individual61/flamingo-repo/Boards/Nano 33 BLE Flamingo/Flamingo Nano 33 BLE Rev 2/Arduino Nano 33 BLE Power Tree.png

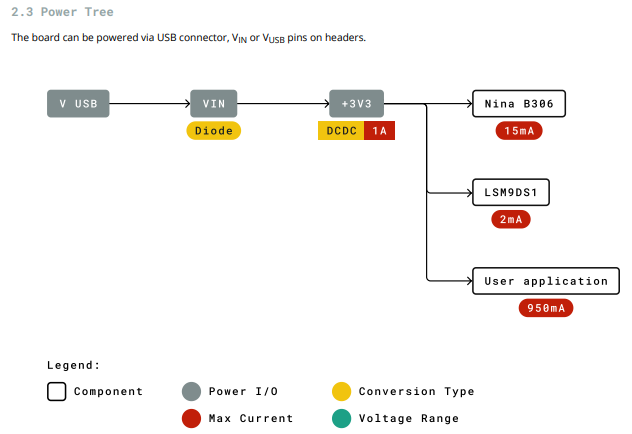
Boards/Nano 33 BLE Flamingo/Flamingo Nano 33 BLE Rev 2/Arduino Nano 33 BLE Power Tree.png
