individual61/flamingo-repo/Boards/Nano 33 BLE Flamingo/Flamingo Nano 33 BLE Rev 2/Nano Power detail 3.png

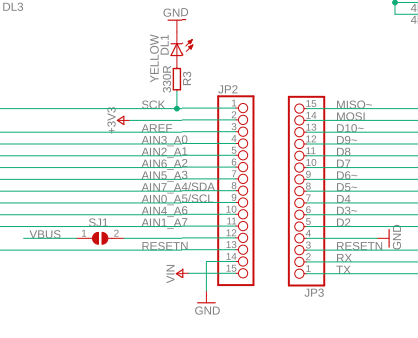
Boards/Nano 33 BLE Flamingo/Flamingo Nano 33 BLE Rev 2/Nano Power detail 3.png
