individual61/flamingo-repo/Boards/Nano 33 BLE Flamingo/Flamingo Nano 33 BLE Rev 2/PDFs/Screenshot 2023-04-27 150545.png

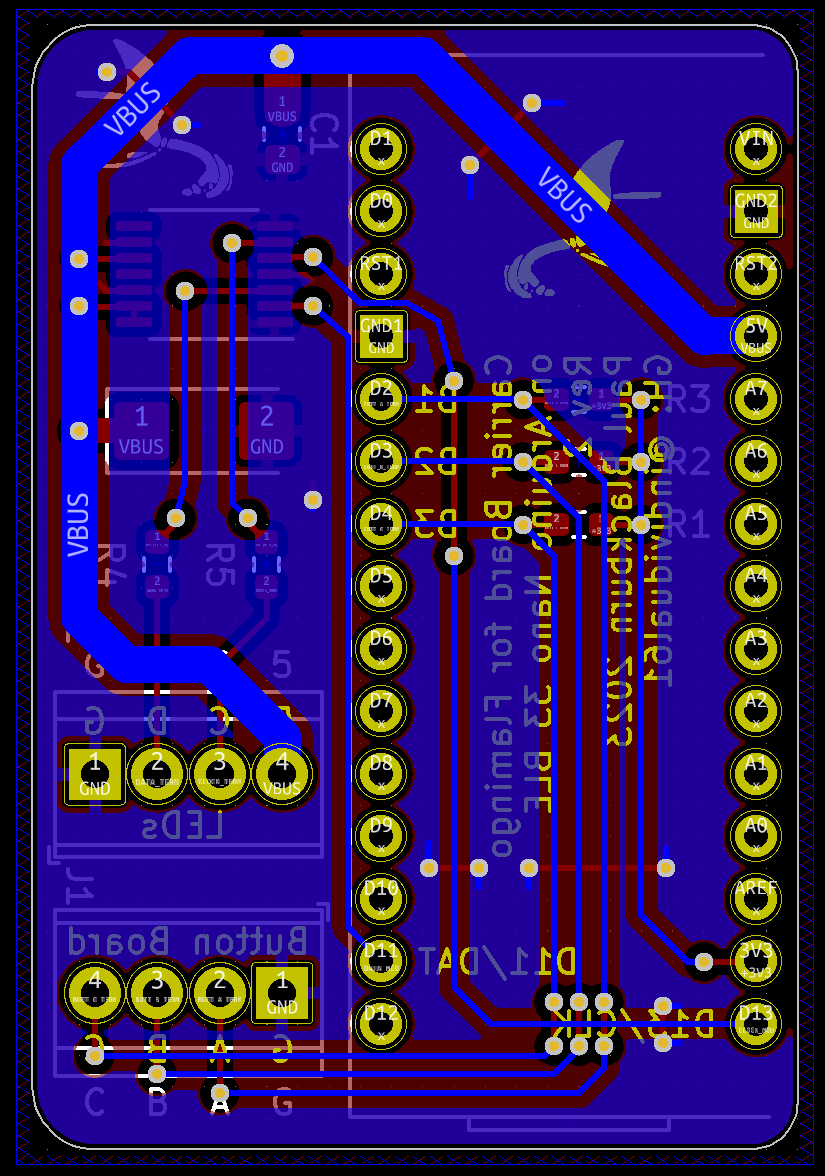
Boards/Nano 33 BLE Flamingo/Flamingo Nano 33 BLE Rev 2/PDFs/Screenshot 2023-04-27 150545.png
