individual61/flamingo-repo/Boards/Nano 33 BLE Flamingo/Flamingo Nano 33 BLE Rev 2/PDFs/Flamingo Nano 33 BLE Rev 2-F_Mask.pdf

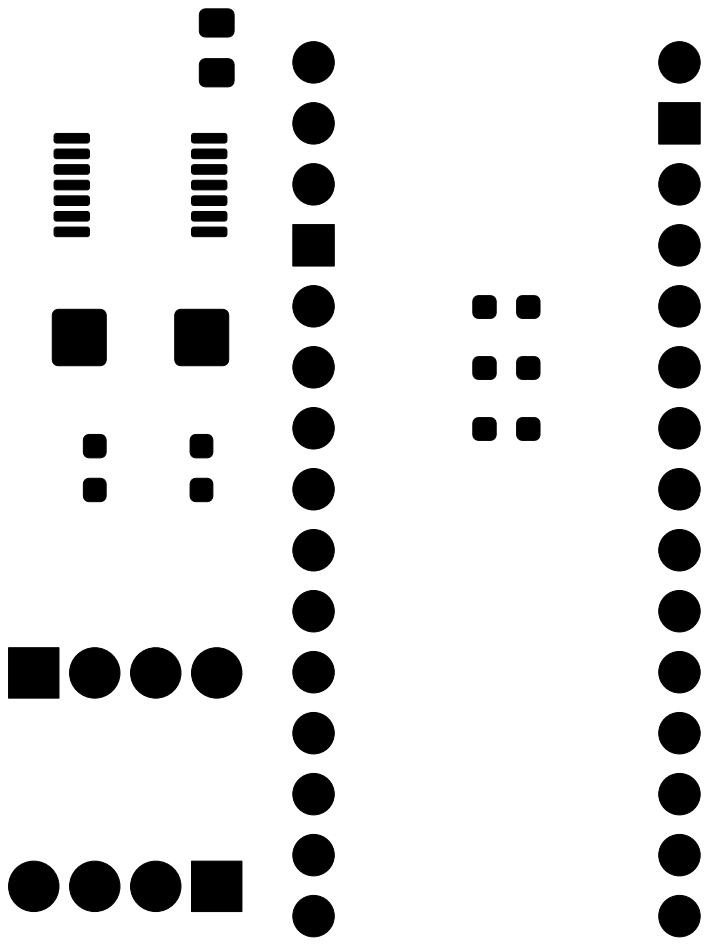
[picture p26: page 1]
