individual61/flamingo-repo/Boards/Nano 33 BLE Flamingo/Flamingo Nano 33 BLE Rev 2/PDFs/Flamingo Nano 33 BLE Rev 2-F_Paste.pdf

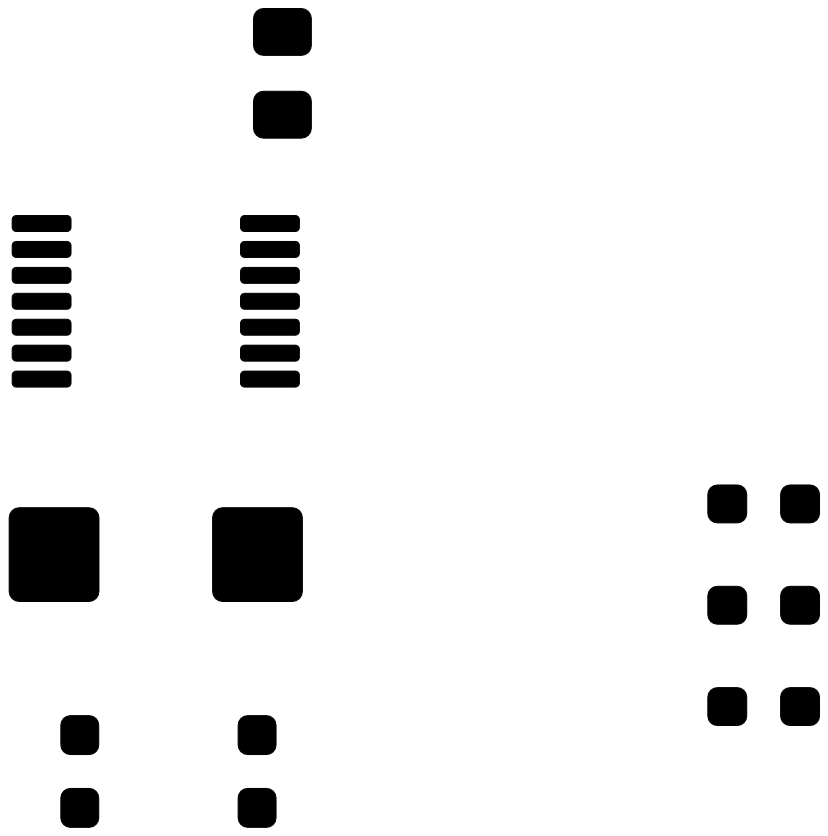
[picture p27: page 1]
