individual61/flamingo-repo/Boards/Nano 33 BLE Flamingo/Flamingo Nano 33 BLE Rev 2/PDFs/Flamingo Nano 33 BLE Rev 2-F_Silkscreen.pdf

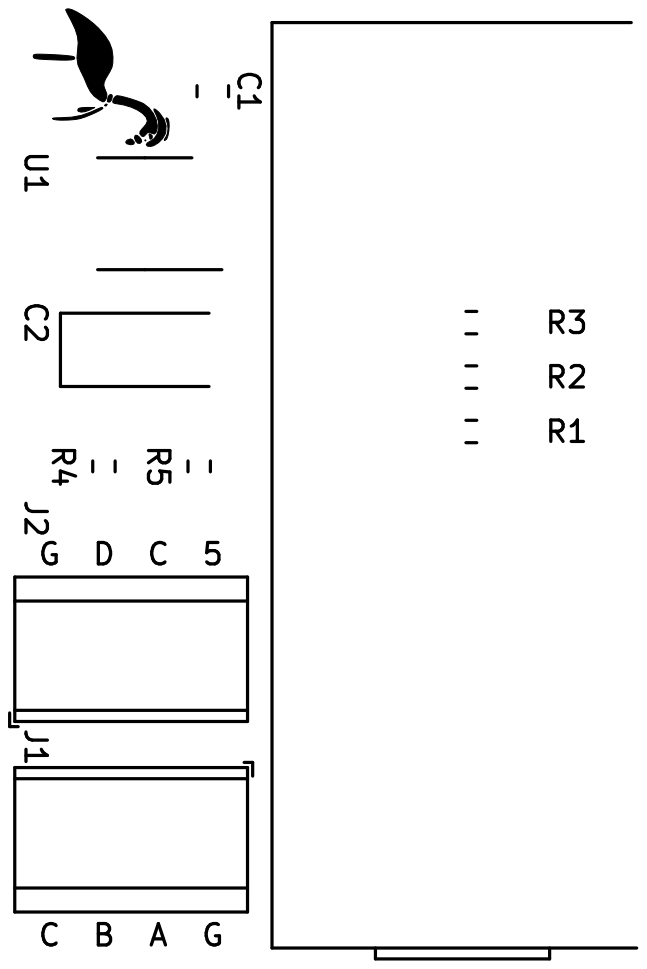
[picture p28: page 1]
