individual61/flamingo-repo/Boards/Flamingo PCBA/Flamingo PCB Rev 3/Flamingo PCB/Power.pdf

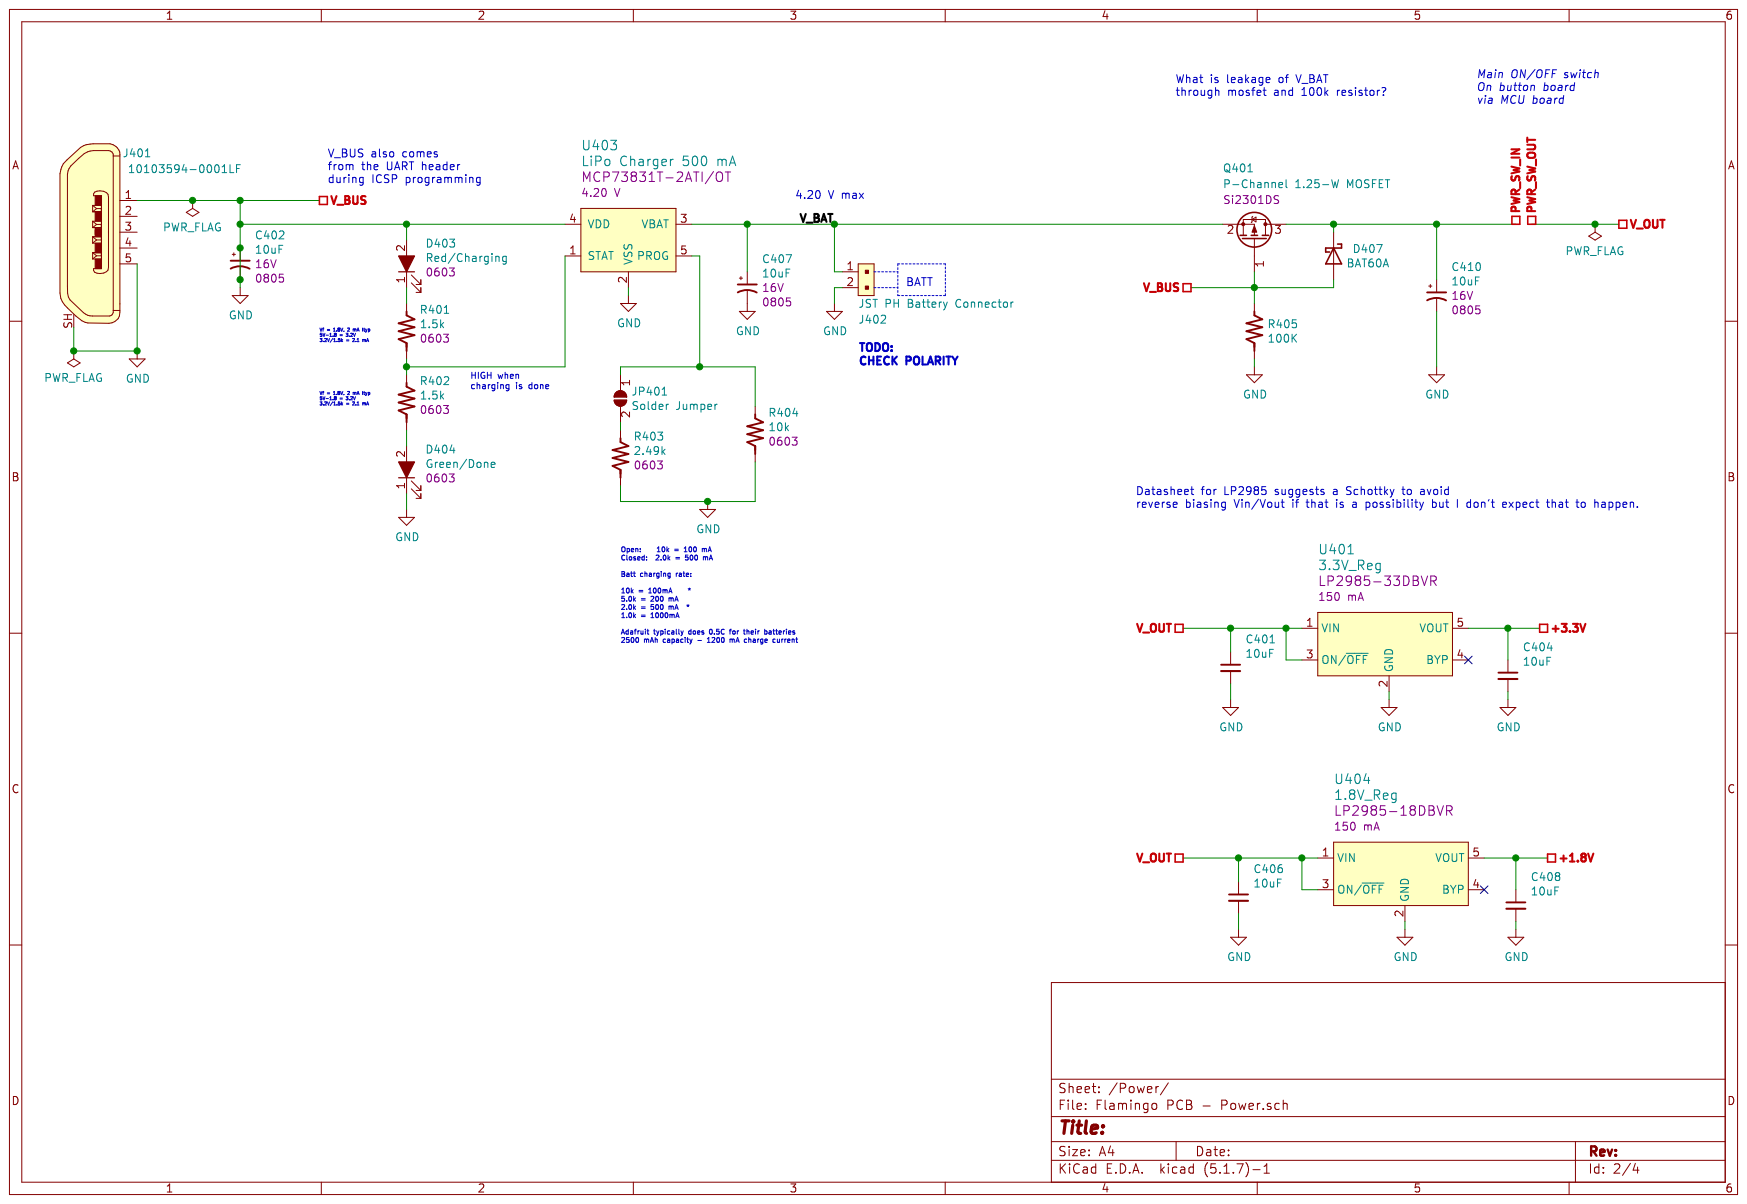
[picture p29: page 1]
