individual61/flamingo-repo/Boards/Flamingo PCBA/Flamingo PCB Rev 3/Flamingo PCB/Flamingo PCB.pdf

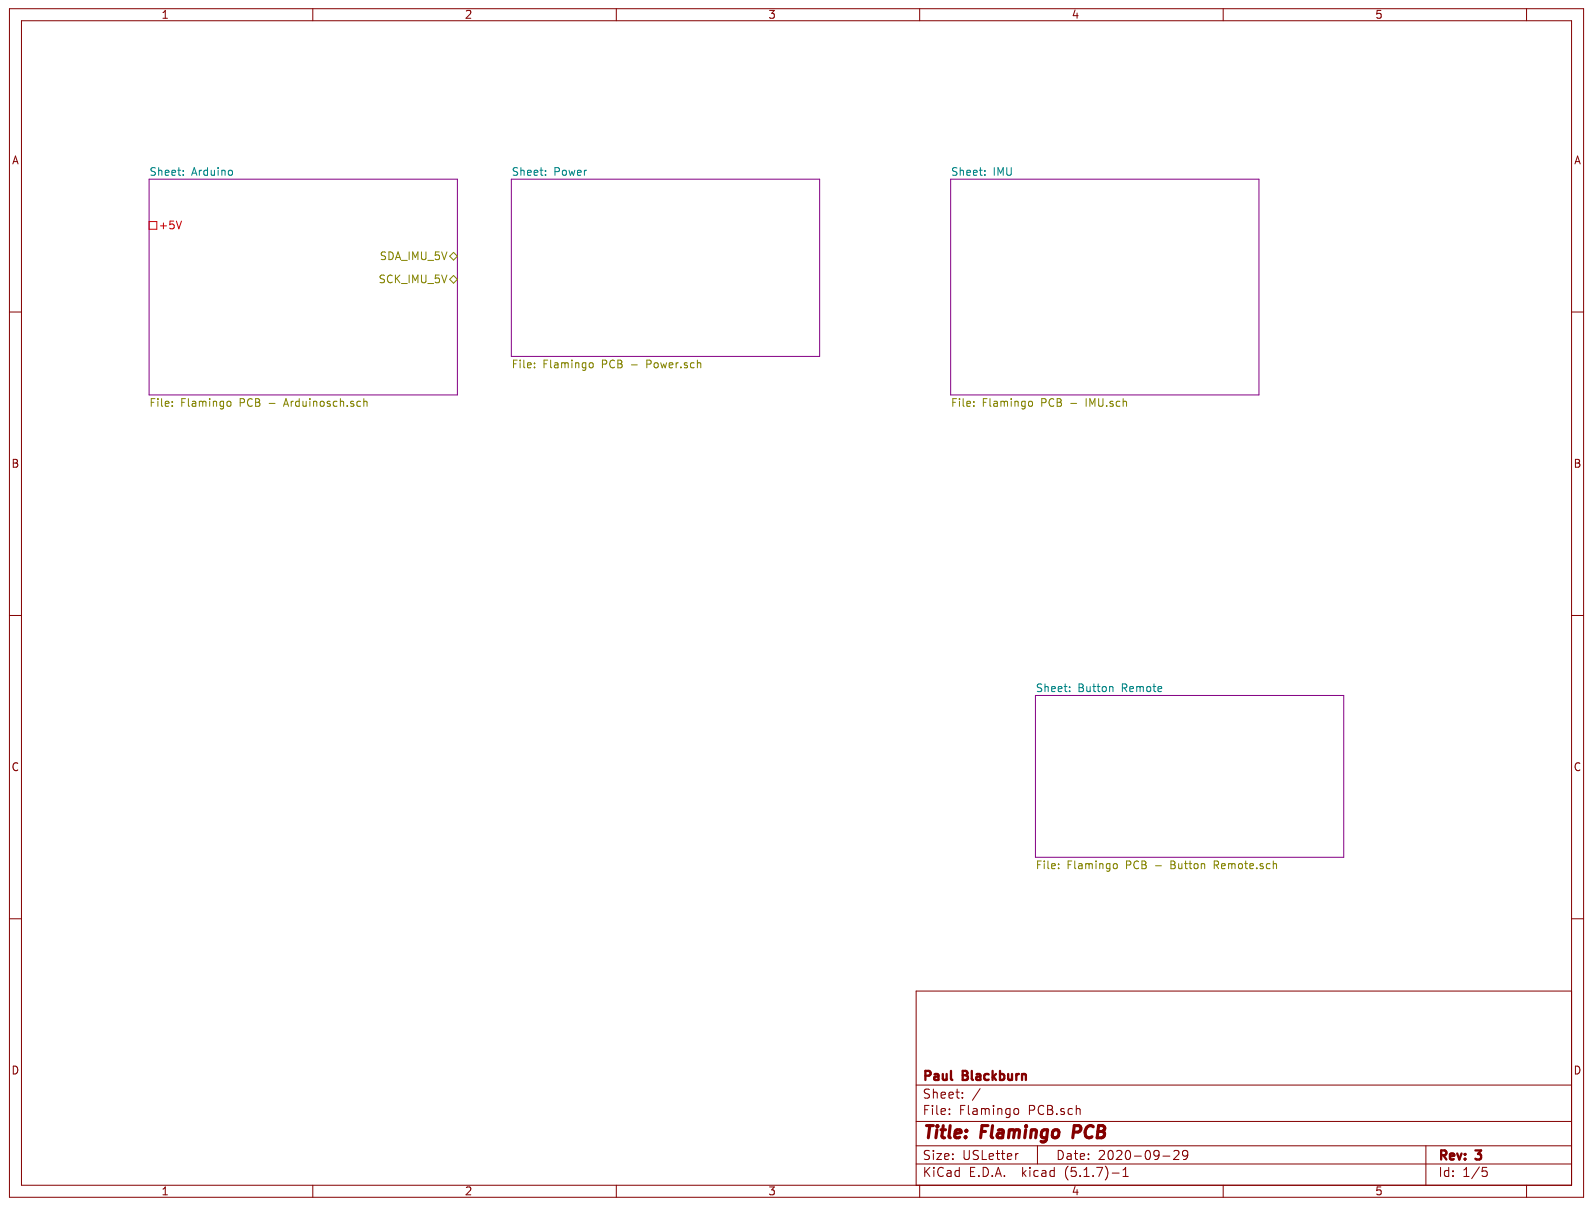
[picture p30: page 1]

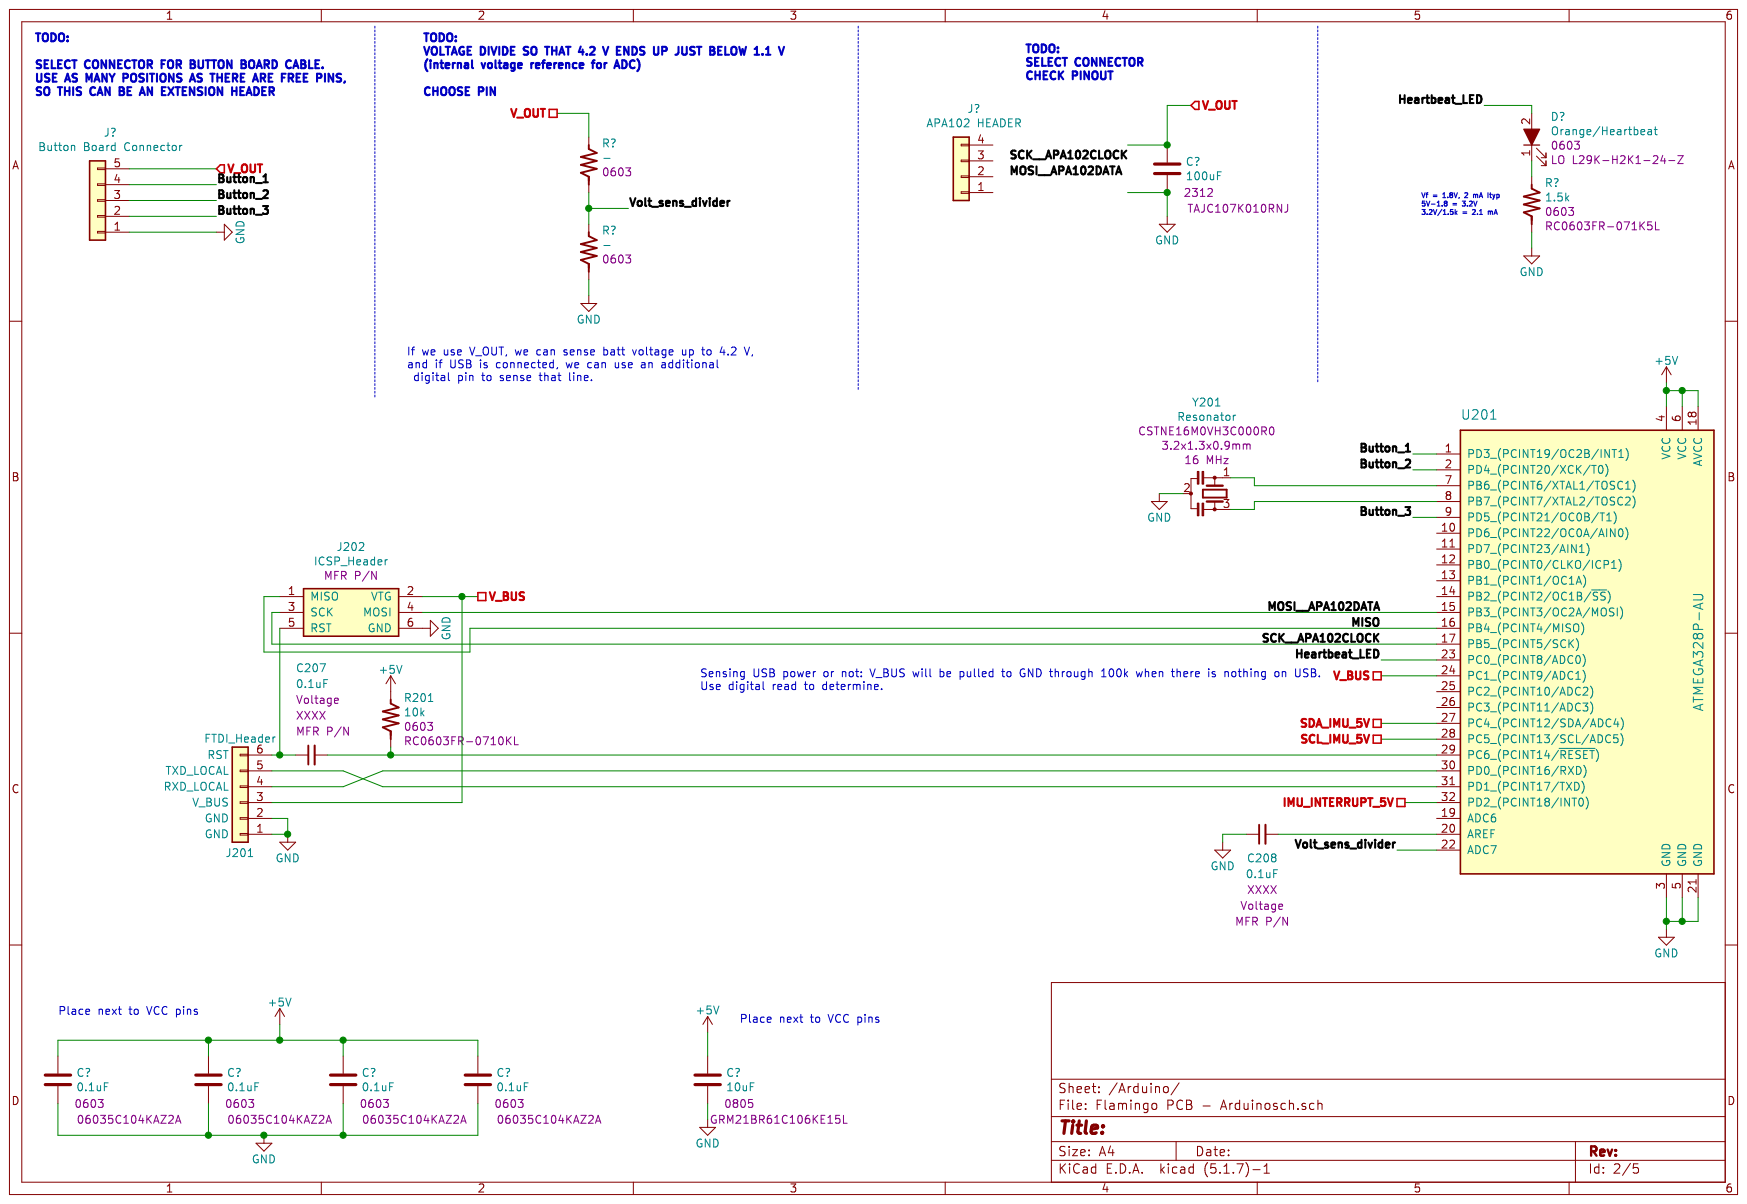
[picture p31: page 2]

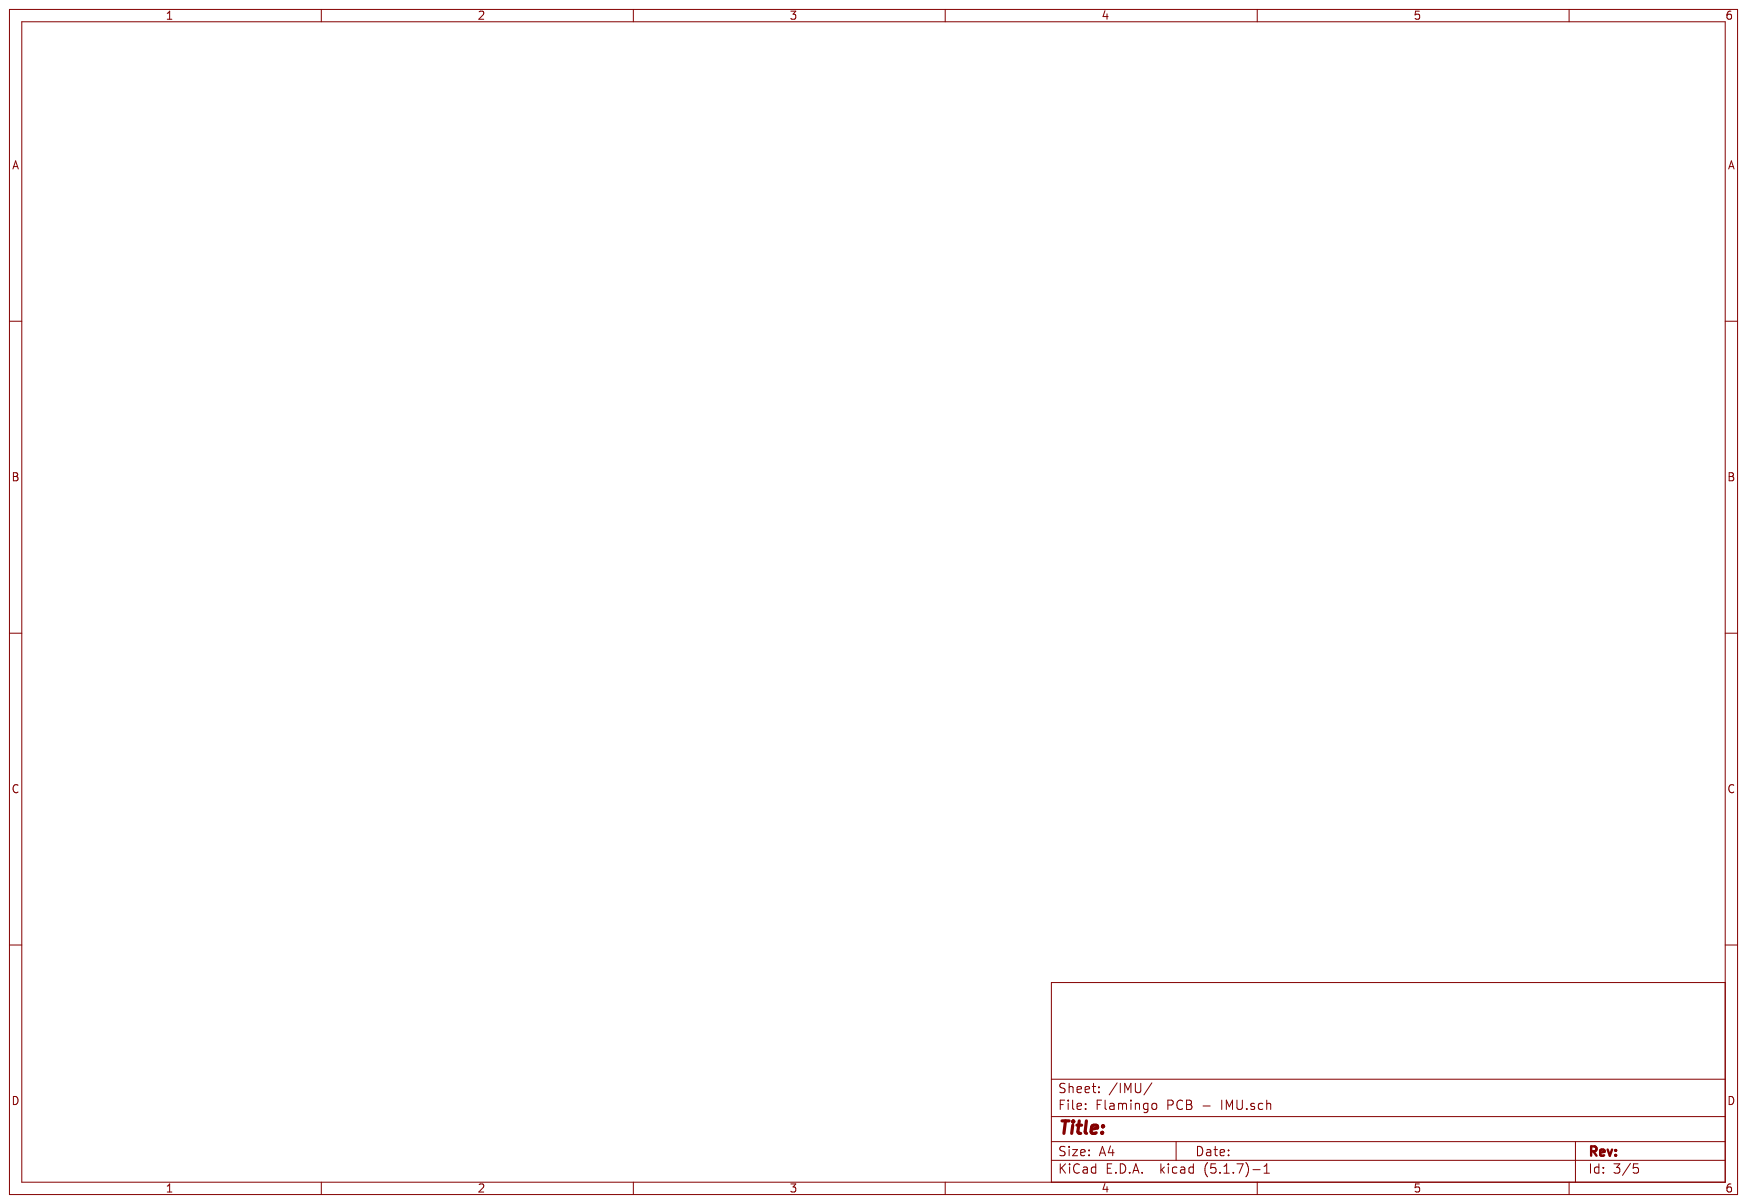
[picture p32: page 3]

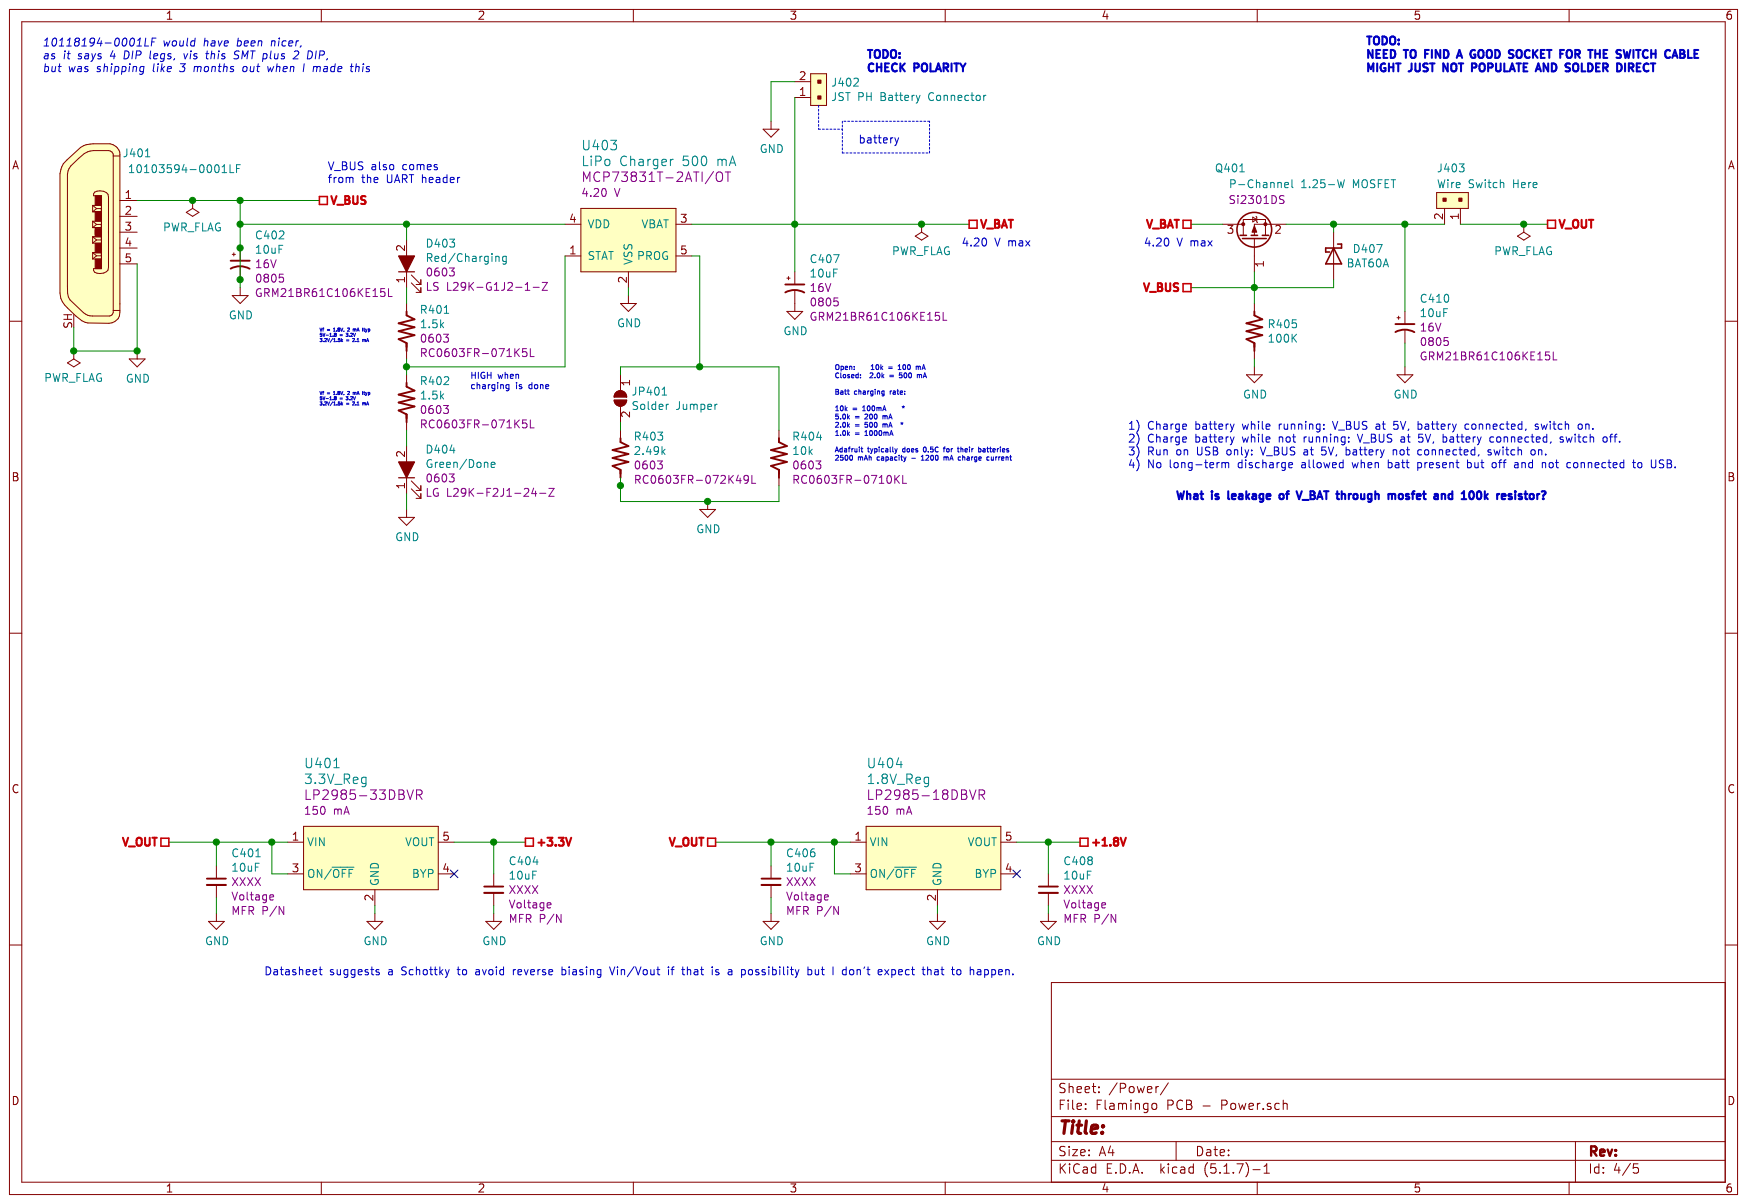
[picture p33: page 4]

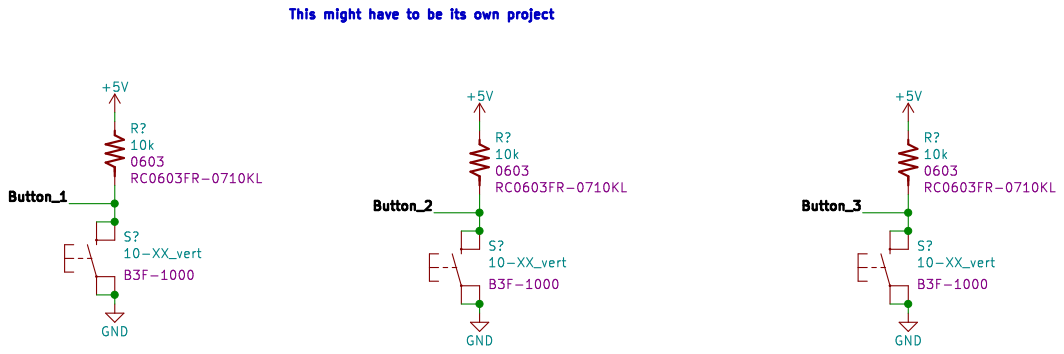
[picture p34: page 5]
