individual61/flamingo-repo/Boards/Bike Flamingo IB-5V-USB/Bike Flamingo IB-5V-USB Rev 1/PDFs/Bike Flamingo for Itsy Bitsy 5V 16MHz, USB Power Rev 1.pdf

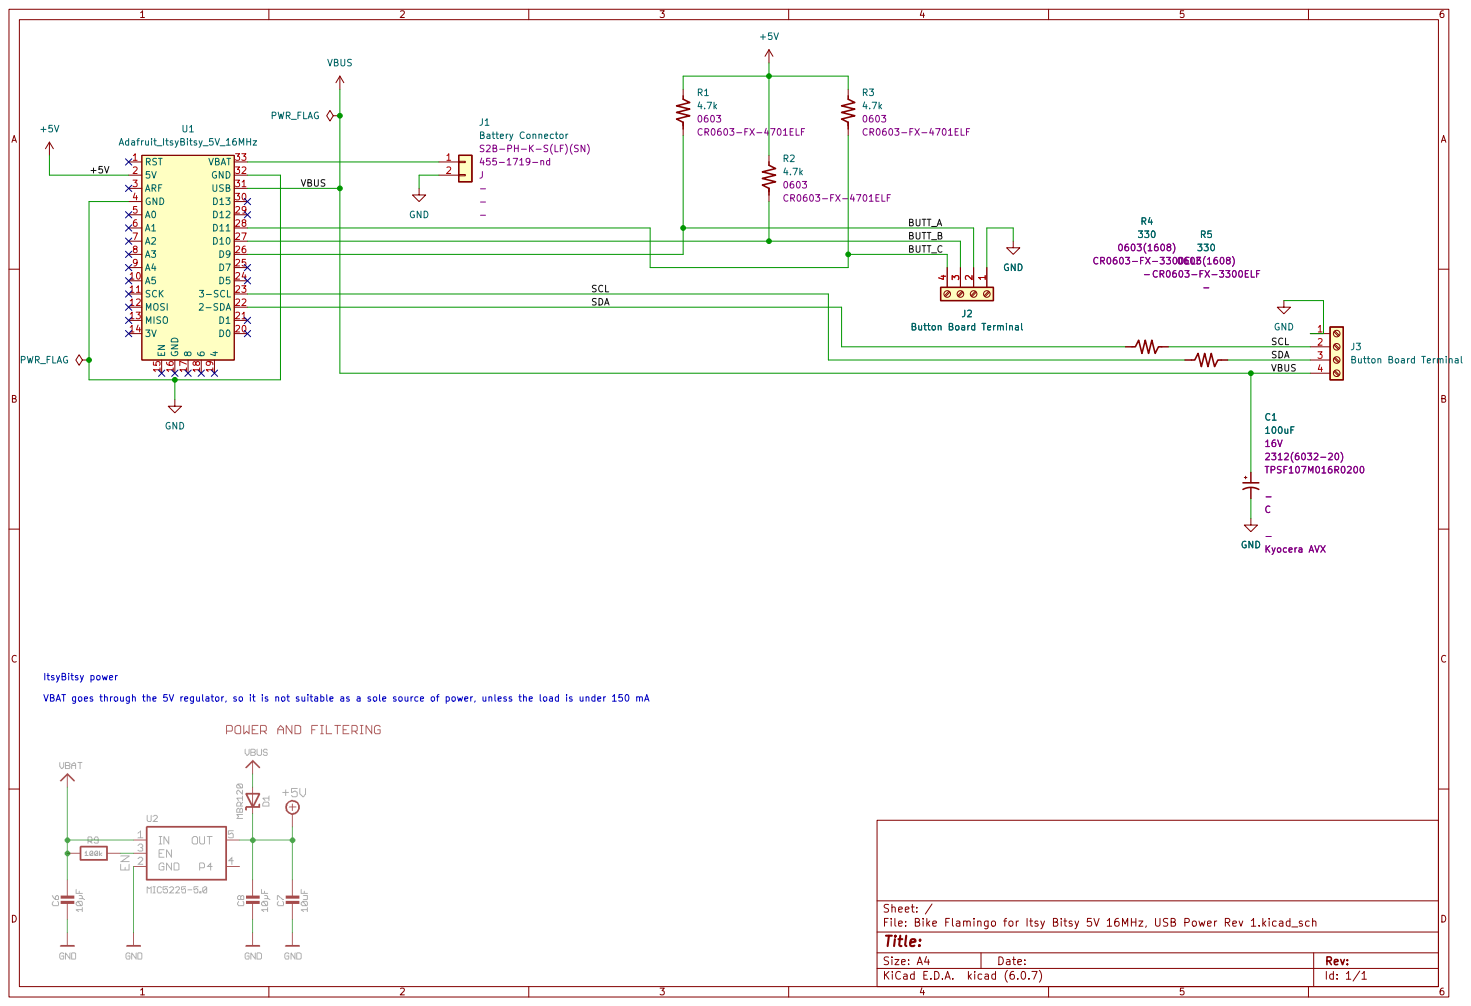
[picture p35: page 1]

Does it make sense to change the LEDs to use VBAT? With VBAT and no USB present, the LEDS get direct battery and the arduino gets regulated output. With USB and no VBAT the LEDs dont see VBUS unless a battery backpack is used. GND

VBAT goes through the 5V regulator, so it is not suitable as a sole source of power, unless the load is under 150 mA
