individual61/flamingo-repo/Boards/Flamingo PCBA/Flamingo PCB Rev 2/inspiration/Adafruit-Pro-Trinket-PCBs-master/Adafruit Pro Trinket 3v3.pdf

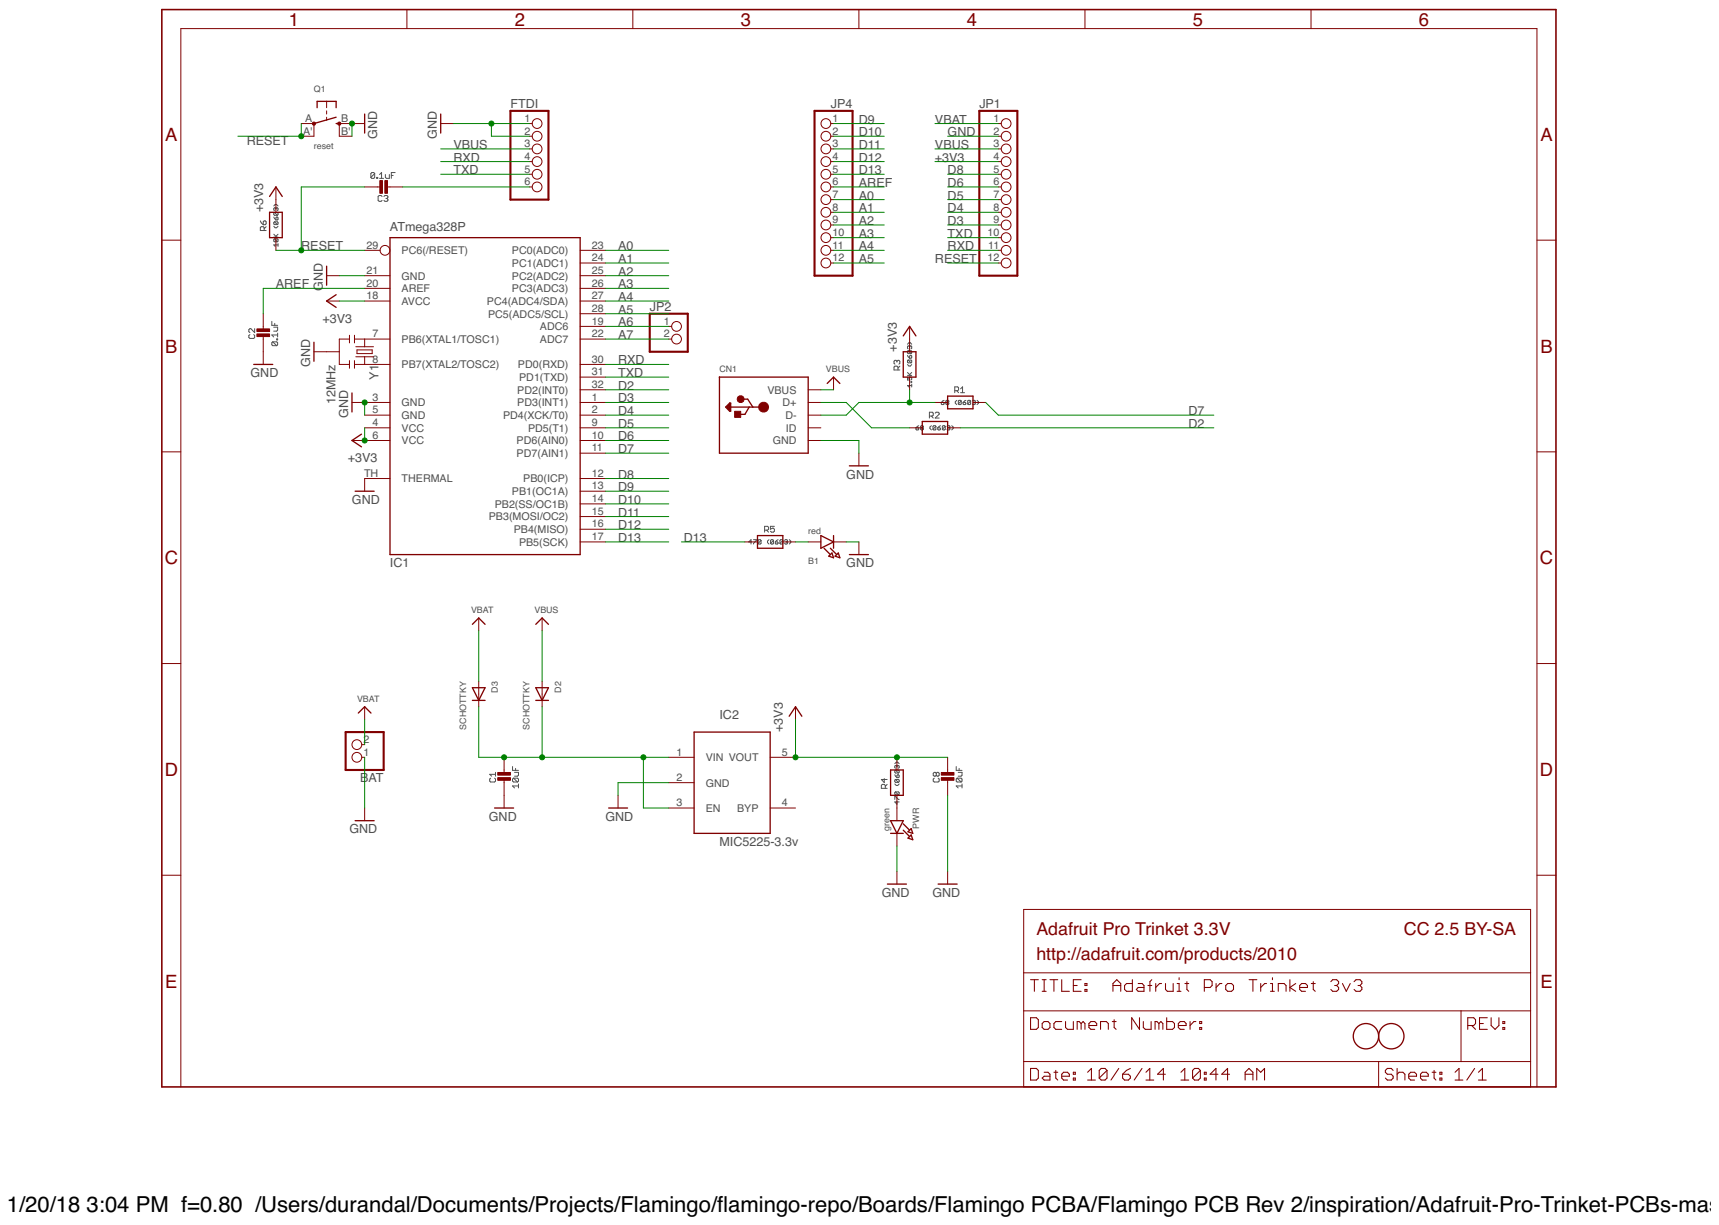
[picture p36: page 1]

Adafruit Pro Trinket 3.3V
http://adafruit.com/products/2010

1/20/18 3:04 PM f=0.80 /Users/durandal/Documents/Projects/Flamingo/flamingo-repo/Boards/Flamingo PCBA/Flamingo PCB Rev 2/inspiration/Adafruit-Pro-Trinket-PCBs-master/Adafruit Pro Trinket 3v3.sch (Sheet: 1/1)
