individual61/flamingo-repo/Boards/Bike Flamingo IB-5V-USB/Bike Flamingo IB-5V-USB Rev 1/PDFs/Board layout.pdf

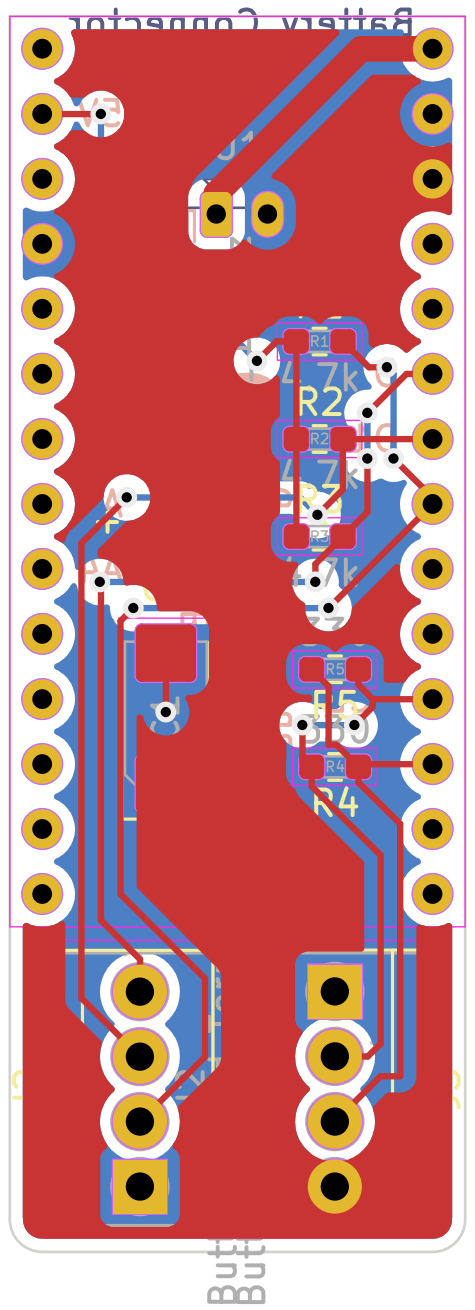
[picture p37: page 1]
