individual61/flamingo-repo/Boards/Flamingo PCBA/Flamingo PCB Rev 1/Flamingo PCB Rev 1.1/Flamingo PCB Rev 1.1.brd

## EAGLE design Boards/Flamingo PCBA/Flamingo PCB Rev 1/Flamingo PCB Rev 1.1/Flamingo PCB Rev 1.1.brd (2017-07-29, an earlier design)

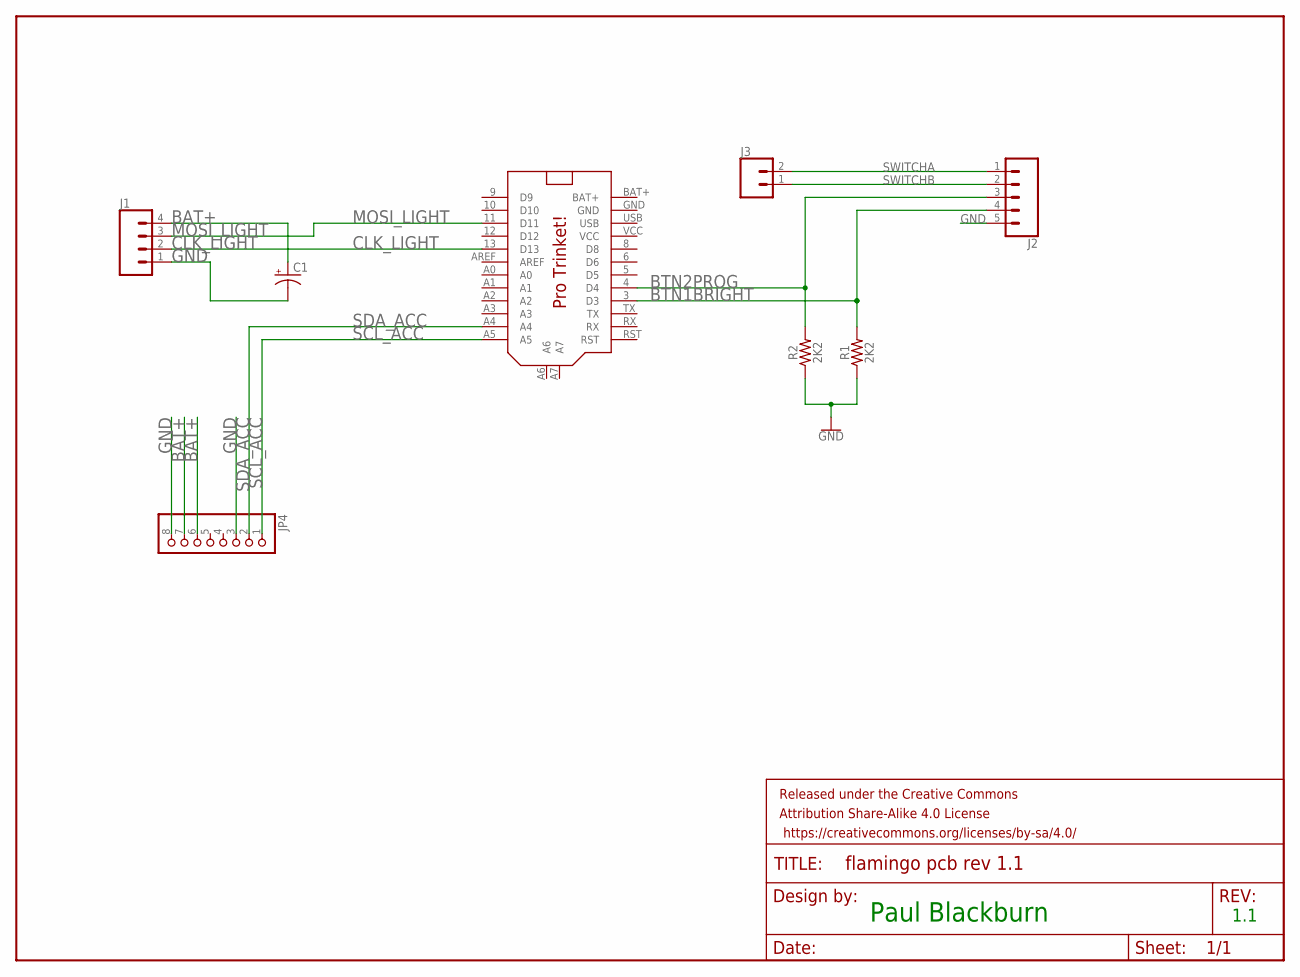
[picture p60: schematic Flamingo PCB Rev 1.1.sch]

Parts:
C1: CPOL-USE5-6; E5-6
FRAME1: FRAME-LETTER; CREATIVE_COMMONS
J1: CONN_04; 1X04
J2: CONN_05; 1X05
J3: CONN_02; 1X02
JP4: PINHD-1X8CLEANBIG; 1X08-CLEANBIG
R1, R2: 2K2; AXIAL-0.3
U$1: PRO_TRINKET; PROTRINKET

Connections:
BAT+: C1.+, J1.4, JP4.6, JP4.7, U$1.BAT+
BTN1BRIGHT: J2.4, R1.P$2 (2), U$1.3 (D3)
BTN2PROG: J2.3, R2.P$2 (2), U$1.4 (D4)
CLK_LIGHT: J1.2, U$1.13 (D13)
GND: C1.-, J1.1, J2.5, JP4.3, JP4.8, R1.P$1 (1), R2.P$1 (1), U$1.GND
MOSI_LIGHT: J1.3, U$1.11 (D11)
SCL_ACC: JP4.1, U$1.A5
SDA_ACC: JP4.2, U$1.A4
SWITCHA: J2.1, J3.2
SWITCHB: J2.2, J3.1
USB: U$1.USB
VCC: U$1.VCC

Notes on the sheet:
Paul Blackburn
1.1

Board: 2 copper layers, 9 parts (0 on the bottom side), 10 nets, no tracks yet.
