individual61/flamingo-repo/Boards/Pixelblaze Flamingo/Ref/PB32_3.x.brd

## EAGLE design Boards/Pixelblaze Flamingo/Ref/PB32_3.x.brd (2023-04-28)

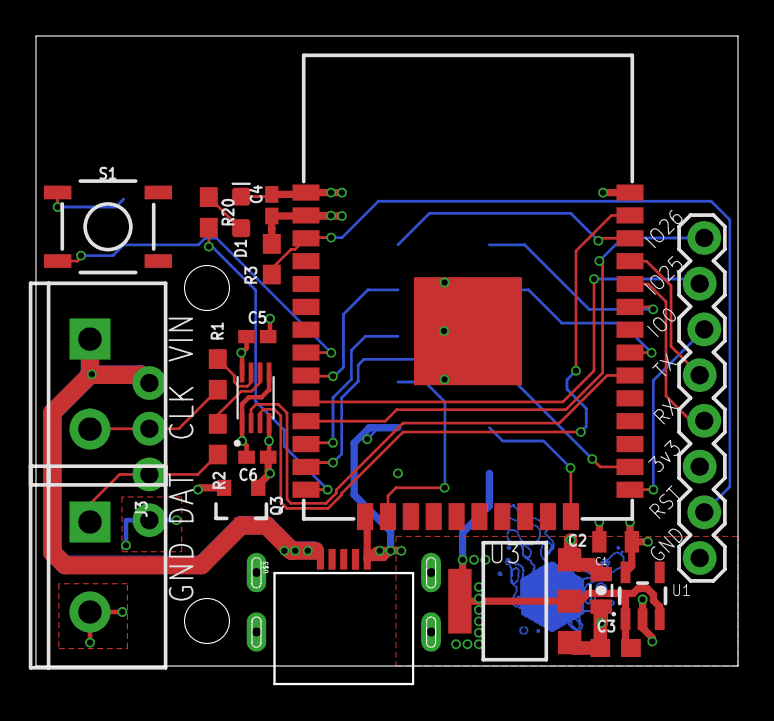
[picture p61: board PB32_3.x.brd from above]

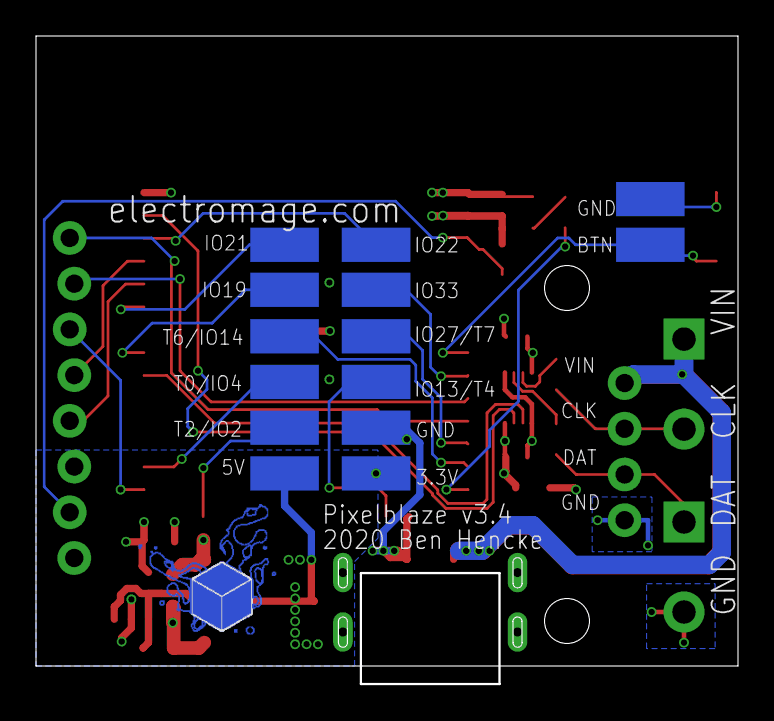
[picture p62: board PB32_3.x.brd from below]

Board: 4 copper layers, 39.0 x 36.0 mm, 37 parts (15 on the bottom side), 29 nets.

Parts:
C1: 1.0uF; 0805-CAP
C2: 10uF; 0805
C3: 4.7uF; 0603
C4, C5, C6: 0.1uF; C0402K
D1: LED-0603
GP1, GP3, GP6, GP8, GP9: PAD
IO2, IO4, IO13, IO14, IO19, IO21, IO22, IO27, IO33: PAD
J1: 1X08_LOCK
J2, J3: SCREWTERMINAL-5MM-2
J4: 1X04_NO_SILK
Q3: 2.5A/30V/105mΩ; SOT23-3
R1, R2, R20: 100; 0603
R3: 1k; 0603
S1: MOMENTARY-SWITCH-SPST-SMD-5.2MM; TACTILE_SWITCH_SMD_5.2MM
U1: AP2112K-3.3TRG1; SOT23-5
U2: ESP-WROOM-32
U3: NX1117C15Z; SOT223
U$1: SN74LVC2T45DCUR; SOP50P310X90-8N
U$2: ELECTRO_MAGE_PCB4_PIXEL_2#PNG
U$3: USB-CON-5PINUSB-SUNK-TIGHT; USB-SUNK-TIGHT

Connections:
+3V3: C2.1, C4.1, C6.1, GP1.P$1, J1.3, R3.2, U1.5, U2.2, U$1.1, U$1.5
+5V: C3.1, C5.1, GP6.P$1, U1.1, U1.3, U3.2, U3.4, U$1.8
BUTTON: GP8.P$1, S1.3, U2.8
EN: J1.2, R3.1, U2.3
GND: C1.2, C2.2, C3.2, C4.2, C5.2, C6.2, D1.C, GP3.P$1, GP9.P$1, J1.1, J3.2, J4.1, Q3.1, S1.1, U1.2, U2.1, U2.15, U2.38, U2.GND, U3.1, U$1.4, U$3.5
IO0: J1.6, U2.25
IO2: IO2.P$1, U2.24
IO4: IO4.P$1, U2.26
IO13: IO13.P$1, U2.16
IO14: IO14.P$1, U2.13
IO19: IO19.P$1, U2.31
IO21: IO21.P$1, U2.33
IO22: IO22.P$1, U2.36
IO25: J1.7, U2.10
IO26: J1.8, U2.11
IO27: IO27.P$1, U2.12
IO33: IO33.P$1, U2.9
LED: R20.2, U2.14
MOSI: U2.37, U$1.3
MOSI_OUT: J3.1, J4.2, R2.2
unnamed: C1.1, Q3.2, U3.3
unnamed: R1.1, U$1.7
unnamed: R2.1, U$1.6
unnamed: D1.A, R20.1
RX: J1.4, U2.34
SCK: U2.30, U$1.2
SCK_OUT: J2.2, J4.3, R1.2
TX: J1.5, U2.35
VIN: J2.1, J4.4, Q3.3, U$3.1
