individual61/flamingo-repo/Boards/Flamingo PCBA/Flamingo PCB Rev 2/inspiration/LiPower_Boost_Converter-master/Production Files/Li_Power_Boost_Converter-Panel-v12B.brd

## EAGLE design Boards/Flamingo PCBA/Flamingo PCB Rev 2/inspiration/LiPower_Boost_Converter-master/Production Files/Li_Power_Boost_Converter-Panel-v12B.brd (2018-02-05, an earlier design)

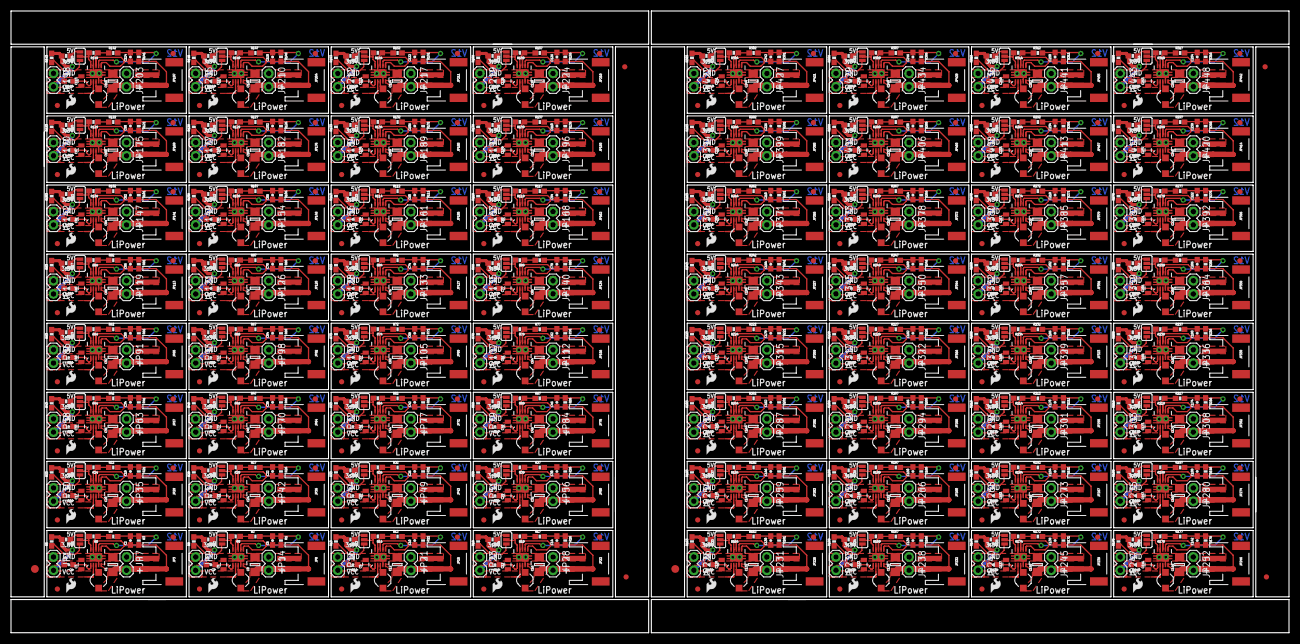
[picture p63: board Li_Power_Boost_Converter-Panel-v12B.brd from above]

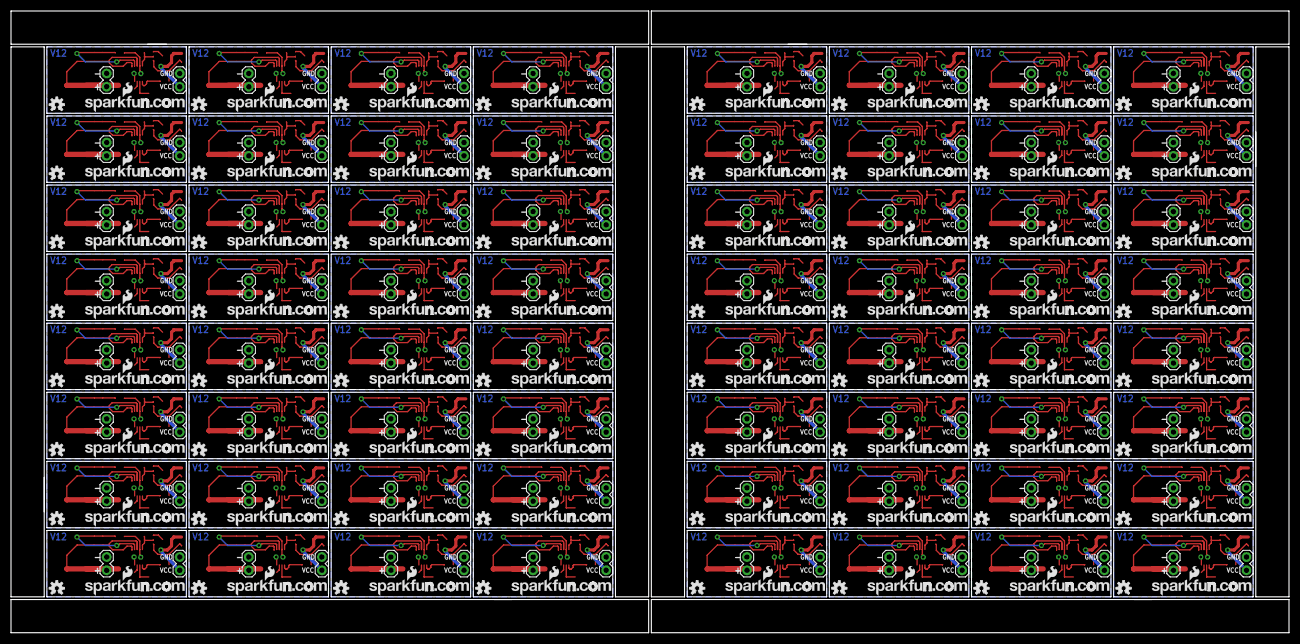
[picture p64: board Li_Power_Boost_Converter-Panel-v12B.brd from below]

Board: 2 copper layers, 244.3 x 118.9 mm, 1286 parts (128 on the bottom side), 576 nets.

Parts:
C1, C8, C12, C16, C20, C24, C28, C32, C36, C40, C44, C48, C52, C56, C60, C64, C68, C72, C76, C80, C84, C88, C92, C96, C100, C104, C108, C112, C116, C120, C124, C128, C132, C136, C140, C144, C148, C152, C156, C160, C164, C168, C172, C176, C180, C184, C188, C192, C196, C200, C204, C208, C212, C216, C220, C224, C228, C232, C236, C240, C244, C248, C252, C256: 10uF; 1206
C2, C4, C6, C7, C10, C11, C14, C15, C18, C19, C22, C23, C26, C27, C30, C31, C34, C35, C38, C39, C42, C43, C46, C47, C50, C51, C54, C55, C58, C59, C62, C63, C66, C67, C70, C71, C74, C75, C78, C79, C82, C83, C86, C87, C90, C91, C94, C95, C98, C99, C102, C103, C106, C107, C110, C111, C114, C115, C118, C119, C122, C123, C126, C127, C130, C131, C134, C135, C138, C139, C142, C143, C146, C147, C150, C151, C154, C155, C158, C159, C162, C163, C166, C167, C170, C171, C174, C175, C178, C179, C182, C183, C186, C187, C190, C191, C194, C195, C198, C199, C202, C203, C206, C207, C210, C211, C214, C215, C218, C219, C222, C223, C226, C227, C230, C231, C234, C235, C238, C239, C242, C243, C246, C247, C250, C251, C254, C255: 0.1uF; 0603-CAP
C3, C5, C9, C13, C17, C21, C25, C29, C33, C37, C41, C45, C49, C53, C57, C61, C65, C69, C73, C77, C81, C85, C89, C93, C97, C101, C105, C109, C113, C117, C121, C125, C129, C133, C137, C141, C145, C149, C153, C157, C161, C165, C169, C173, C177, C181, C185, C189, C193, C197, C201, C205, C209, C213, C217, C221, C225, C229, C233, C237, C241, C245, C249, C253: 22uF; 0805
E$1, E$6: FIDUCIAL-1.5X3
E$2, E$3, E$4, E$5: FIDUCIAL-1X2
JP1, JP9, JP16, JP23, JP30, JP37, JP44, JP51, JP58, JP65, JP72, JP79, JP86, JP93, JP100, JP107, JP114, JP121, JP128, JP135, JP142, JP149, JP156, JP163, JP170, JP177, JP184, JP191, JP198, JP205, JP212, JP219, JP226, JP233, JP240, JP247, JP254, JP261, JP268, JP275, JP282, JP289, JP296, JP303, JP310, JP317, JP324, JP331, JP338, JP345, JP352, JP359, JP366, JP373, JP380, JP387, JP394, JP401, JP408, JP415, JP422, JP429, JP436, JP443: VOUT; 1X02
JP2, JP10, JP17, JP24, JP31, JP38, JP45, JP52, JP59, JP66, JP73, JP80, JP87, JP94, JP101, JP108, JP115, JP122, JP129, JP136, JP143, JP150, JP157, JP164, JP171, JP178, JP185, JP192, JP199, JP206, JP213, JP220, JP227, JP234, JP241, JP248, JP255, JP262, JP269, JP276, JP283, JP290, JP297, JP304, JP311, JP318, JP325, JP332, JP339, JP346, JP353, JP360, JP367, JP374, JP381, JP388, JP395, JP402, JP409, JP416, JP423, JP430, JP437, JP444: LOGO-SFESK; SFE-LOGO-FLAME
JP3, JP8, JP15, JP22, JP29, JP36, JP43, JP50, JP57, JP64, JP71, JP78, JP85, JP92, JP99, JP106, JP113, JP120, JP127, JP134, JP141, JP148, JP155, JP162, JP169, JP176, JP183, JP190, JP197, JP204, JP211, JP218, JP225, JP232, JP239, JP246, JP253, JP260, JP267, JP274, JP281, JP288, JP295, JP302, JP309, JP316, JP323, JP330, JP337, JP344, JP351, JP358, JP365, JP372, JP379, JP386, JP393, JP400, JP407, JP414, JP421, JP428, JP435, JP442: JST; JST-2-SMD
JP4, JP5, JP11, JP12, JP18, JP19, JP25, JP26, JP32, JP33, JP39, JP40, JP46, JP47, JP53, JP54, JP60, JP61, JP67, JP68, JP74, JP75, JP81, JP82, JP88, JP89, JP95, JP96, JP102, JP103, JP109, JP110, JP116, JP117, JP123, JP124, JP130, JP131, JP137, JP138, JP144, JP145, JP151, JP152, JP158, JP159, JP165, JP166, JP172, JP173, JP179, JP180, JP186, JP187, JP193, JP194, JP200, JP201, JP207, JP208, JP214, JP215, JP221, JP222, JP228, JP229, JP235, JP236, JP242, JP243, JP249, JP250, JP256, JP257, JP263, JP264, JP270, JP271, JP277, JP278, JP284, JP285, JP291, JP292, JP298, JP299, JP305, JP306, JP312, JP313, JP319, JP320, JP326, JP327, JP333, JP334, JP340, JP341, JP347, JP348, JP354, JP355, JP361, JP362, JP368, JP369, JP375, JP376, JP382, JP383, JP389, JP390, JP396, JP397, JP403, JP404, JP410, JP411, JP417, JP418, JP424, JP425, JP431, JP432, JP438, JP439, JP445, JP446: FIDUCIAL1X2; FIDUCIAL-1X2
JP6, JP13, JP20, JP27, JP34, JP41, JP48, JP55, JP62, JP69, JP76, JP83, JP90, JP97, JP104, JP111, JP118, JP125, JP132, JP139, JP146, JP153, JP160, JP167, JP174, JP181, JP188, JP195, JP202, JP209, JP216, JP223, JP230, JP237, JP244, JP251, JP258, JP265, JP272, JP279, JP286, JP293, JP300, JP307, JP314, JP321, JP328, JP335, JP342, JP349, JP356, JP363, JP370, JP377, JP384, JP391, JP398, JP405, JP412, JP419, JP426, JP433, JP440, JP447: LOGO-SFENEW; SFE-NEW-WEBLOGO
JP7, JP14, JP21, JP28, JP35, JP42, JP49, JP56, JP63, JP70, JP77, JP84, JP91, JP98, JP105, JP112, JP119, JP126, JP133, JP140, JP147, JP154, JP161, JP168, JP175, JP182, JP189, JP196, JP203, JP210, JP217, JP224, JP231, JP238, JP245, JP252, JP259, JP266, JP273, JP280, JP287, JP294, JP301, JP308, JP315, JP322, JP329, JP336, JP343, JP350, JP357, JP364, JP371, JP378, JP385, JP392, JP399, JP406, JP413, JP420, JP427, JP434, JP441, JP448: VIN; 1X02
L1, L2, L3, L4, L5, L6, L7, L8, L9, L10, L11, L12, L13, L14, L15, L16, L17, L18, L19, L20, L21, L22, L23, L24, L25, L26, L27, L28, L29, L30, L31, L32, L33, L34, L35, L36, L37, L38, L39, L40, L41, L42, L43, L44, L45, L46, L47, L48, L49, L50, L51, L52, L53, L54, L55, L56, L57, L58, L59, L60, L61, L62, L63, L64: 4.7uH, 1.2A; CDRH2D09
R1, R3, R7, R10, R11, R15, R16, R20, R21, R25, R26, R30, R31, R35, R36, R40, R41, R45, R46, R50, R51, R55, R56, R60, R61, R65, R66, R70, R71, R75, R76, R80, R81, R85, R86, R90, R91, R95, R96, R100, R101, R105, R106, R110, R111, R115, R116, R120, R121, R125, R126, R130, R131, R135, R136, R140, R141, R145, R146, R150, R151, R155, R156, R160, R161, R165, R166, R170, R171, R175, R176, R180, R181, R185, R186, R190, R191, R195, R196, R200, R201, R205, R206, R210, R211, R215, R216, R220, R221, R225, R226, R230, R231, R235, R236, R240, R241, R245, R246, R250, R251, R255, R256, R260, R261, R265, R266, R270, R271, R275, R276, R280, R281, R285, R286, R290, R291, R295, R296, R300, R301, R305, R306, R310, R311, R315, R316, R320: 2M; 0603-RES
R2, R4, R6, R9, R12, R14, R17, R19, R22, R24, R27, R29, R32, R34, R37, R39, R42, R44, R47, R49, R52, R54, R57, R59, R62, R64, R67, R69, R72, R74, R77, R79, R82, R84, R87, R89, R92, R94, R97, R99, R102, R104, R107, R109, R112, R114, R117, R119, R122, R124, R127, R129, R132, R134, R137, R139, R142, R144, R147, R149, R152, R154, R157, R159, R162, R164, R167, R169, R172, R174, R177, R179, R182, R184, R187, R189, R192, R194, R197, R199, R202, R204, R207, R209, R212, R214, R217, R219, R222, R224, R227, R229, R232, R234, R237, R239, R242, R244, R247, R249, R252, R254, R257, R259, R262, R264, R267, R269, R272, R274, R277, R279, R282, R284, R287, R289, R292, R294, R297, R299, R302, R304, R307, R309, R312, R314, R317, R319: 220k; 0603-RES
R5, R8, R13, R18, R23, R28, R33, R38, R43, R48, R53, R58, R63, R68, R73, R78, R83, R88, R93, R98, R103, R108, R113, R118, R123, R128, R133, R138, R143, R148, R153, R158, R163, R168, R173, R178, R183, R188, R193, R198, R203, R208, R213, R218, R223, R228, R233, R238, R243, R248, R253, R258, R263, R268, R273, R278, R283, R288, R293, R298, R303, R308, R313, R318: 1.2M; 0603-RES
SJ1, SJ2, SJ3, SJ4, SJ5, SJ6, SJ7, SJ8, SJ9, SJ10, SJ11, SJ12, SJ13, SJ14, SJ15, SJ16, SJ17, SJ18, SJ19, SJ20, SJ21, SJ22, SJ23, SJ24, SJ25, SJ26, SJ27, SJ28, SJ29, SJ30, SJ31, SJ32, SJ33, SJ34, SJ35, SJ36, SJ37, SJ38, SJ39, SJ40, SJ41, SJ42, SJ43, SJ44, SJ45, SJ46, SJ47, SJ48, SJ49, SJ50, SJ51, SJ52, SJ53, SJ54, SJ55, SJ56, SJ57, SJ58, SJ59, SJ60, SJ61, SJ62, SJ63, SJ64: SJ_3_PASTE2&3
U1, U2, U3, U4, U5, U6, U7, U8, U9, U10, U11, U12, U13, U14, U15, U16, U17, U18, U19, U20, U21, U22, U23, U24, U25, U26, U27, U28, U29, U30, U31, U32, U33, U34, U35, U36, U37, U38, U39, U40, U41, U42, U43, U44, U45, U46, U47, U48, U49, U50, U51, U52, U53, U54, U55, U56, U57, U58, U59, U60, U61, U62, U63, U64: TPS61200; QFN-10_PAD
U$1, U$2, U$3, U$4, U$5, U$6, U$7, U$8, U$9, U$10, U$11, U$12, U$13, U$14, U$15, U$16, U$17, U$18, U$19, U$20, U$21, U$22, U$23, U$24, U$25, U$26, U$27, U$28, U$29, U$30, U$31, U$32, U$33, U$34, U$35, U$36, U$37, U$38, U$39, U$40, U$41, U$42, U$43, U$44, U$45, U$46, U$47, U$48, U$49, U$50, U$51, U$52, U$53, U$54, U$55, U$56, U$57, U$58, U$59, U$60, U$61, U$62, U$63, U$64: OSHW-LOGO-S

Connections:
3.3V: R5.1, SJ1.1
3.3V1: R8.1, SJ2.1
3.3V2: R13.1, SJ3.1
3.3V3: R18.1, SJ4.1
3.3V4: R23.1, SJ5.1
3.3V5: R28.1, SJ6.1
3.3V6: R33.1, SJ7.1
3.3V7: R38.1, SJ8.1
3.3V8: R43.1, SJ9.1
3.3V9: R48.1, SJ10.1
3.3V10: R53.1, SJ11.1
3.3V11: R58.1, SJ12.1
3.3V12: R63.1, SJ13.1
3.3V13: R68.1, SJ14.1
3.3V14: R73.1, SJ15.1
3.3V15: R78.1, SJ16.1
3.3V16: R83.1, SJ17.1
3.3V17: R88.1, SJ18.1
3.3V18: R93.1, SJ19.1
3.3V19: R98.1, SJ20.1
3.3V20: R103.1, SJ21.1
3.3V21: R108.1, SJ22.1
3.3V22: R113.1, SJ23.1
3.3V23: R118.1, SJ24.1
3.3V24: R123.1, SJ25.1
3.3V25: R128.1, SJ26.1
3.3V26: R133.1, SJ27.1
3.3V27: R138.1, SJ28.1
3.3V28: R143.1, SJ29.1
3.3V29: R148.1, SJ30.1
3.3V30: R153.1, SJ31.1
3.3V31: R158.1, SJ32.1
3.3V32: R163.1, SJ33.1
3.3V33: R168.1, SJ34.1
3.3V34: R173.1, SJ35.1
3.3V35: R178.1, SJ36.1
3.3V36: R183.1, SJ37.1
3.3V37: R188.1, SJ38.1
3.3V38: R193.1, SJ39.1
3.3V39: R198.1, SJ40.1
3.3V40: R203.1, SJ41.1
3.3V41: R208.1, SJ42.1
3.3V42: R213.1, SJ43.1
3.3V43: R218.1, SJ44.1
3.3V44: R223.1, SJ45.1
3.3V45: R228.1, SJ46.1
3.3V46: R233.1, SJ47.1
3.3V47: R238.1, SJ48.1
3.3V48: R243.1, SJ49.1
3.3V49: R248.1, SJ50.1
3.3V50: R253.1, SJ51.1
3.3V51: R258.1, SJ52.1
3.3V52: R263.1, SJ53.1
3.3V53: R268.1, SJ54.1
3.3V54: R273.1, SJ55.1
3.3V55: R278.1, SJ56.1
3.3V56: R283.1, SJ57.1
3.3V57: R288.1, SJ58.1
3.3V58: R293.1, SJ59.1
3.3V59: R298.1, SJ60.1
3.3V60: R303.1, SJ61.1
3.3V61: R308.1, SJ62.1
3.3V62: R313.1, SJ63.1
3.3V63: R318.1, SJ64.1
5V: R7.1, SJ1.3
5V1: R10.1, SJ2.3
5V2: R15.1, SJ3.3
5V3: R20.1, SJ4.3
5V4: R25.1, SJ5.3
5V5: R30.1, SJ6.3
5V6: R35.1, SJ7.3
5V7: R40.1, SJ8.3
5V8: R45.1, SJ9.3
5V9: R50.1, SJ10.3
5V10: R55.1, SJ11.3
5V11: R60.1, SJ12.3
5V12: R65.1, SJ13.3
5V13: R70.1, SJ14.3
5V14: R75.1, SJ15.3
5V15: R80.1, SJ16.3
5V16: R85.1, SJ17.3
5V17: R90.1, SJ18.3
5V18: R95.1, SJ19.3
5V19: R100.1, SJ20.3
5V20: R105.1, SJ21.3
5V21: R110.1, SJ22.3
5V22: R115.1, SJ23.3
5V23: R120.1, SJ24.3
5V24: R125.1, SJ25.3
5V25: R130.1, SJ26.3
5V26: R135.1, SJ27.3
5V27: R140.1, SJ28.3
5V28: R145.1, SJ29.3
5V29: R150.1, SJ30.3
5V30: R155.1, SJ31.3
5V31: R160.1, SJ32.3
5V32: R165.1, SJ33.3
5V33: R170.1, SJ34.3
5V34: R175.1, SJ35.3
5V35: R180.1, SJ36.3
5V36: R185.1, SJ37.3
5V37: R190.1, SJ38.3
5V38: R195.1, SJ39.3
5V39: R200.1, SJ40.3
5V40: R205.1, SJ41.3
5V41: R210.1, SJ42.3
5V42: R215.1, SJ43.3
5V43: R220.1, SJ44.3
5V44: R225.1, SJ45.3
5V45: R230.1, SJ46.3
5V46: R235.1, SJ47.3
5V47: R240.1, SJ48.3
5V48: R245.1, SJ49.3
5V49: R250.1, SJ50.3
5V50: R255.1, SJ51.3
5V51: R260.1, SJ52.3
5V52: R265.1, SJ53.3
5V53: R270.1, SJ54.3
5V54: R275.1, SJ55.3
5V55: R280.1, SJ56.3
5V56: R285.1, SJ57.3
5V57: R290.1, SJ58.3
5V58: R295.1, SJ59.3
5V59: R300.1, SJ60.3
5V60: R305.1, SJ61.3
5V61: R310.1, SJ62.3
5V62: R315.1, SJ63.3
5V63: R320.1, SJ64.3
FB: R6.2, SJ1.2, U1.10
FB1: R9.2, SJ2.2, U2.10
FB2: R14.2, SJ3.2, U3.10
FB3: R19.2, SJ4.2, U4.10
FB4: R24.2, SJ5.2, U5.10
FB5: R29.2, SJ6.2, U6.10
FB6: R34.2, SJ7.2, U7.10
FB7: R39.2, SJ8.2, U8.10
FB8: R44.2, SJ9.2, U9.10
FB9: R49.2, SJ10.2, U10.10
FB10: R54.2, SJ11.2, U11.10
FB11: R59.2, SJ12.2, U12.10
FB12: R64.2, SJ13.2, U13.10
FB13: R69.2, SJ14.2, U14.10
FB14: R74.2, SJ15.2, U15.10
FB15: R79.2, SJ16.2, U16.10
FB16: R84.2, SJ17.2, U17.10
FB17: R89.2, SJ18.2, U18.10
FB18: R94.2, SJ19.2, U19.10
FB19: R99.2, SJ20.2, U20.10
FB20: R104.2, SJ21.2, U21.10
FB21: R109.2, SJ22.2, U22.10
FB22: R114.2, SJ23.2, U23.10
FB23: R119.2, SJ24.2, U24.10
FB24: R124.2, SJ25.2, U25.10
FB25: R129.2, SJ26.2, U26.10
FB26: R134.2, SJ27.2, U27.10
FB27: R139.2, SJ28.2, U28.10
FB28: R144.2, SJ29.2, U29.10
FB29: R149.2, SJ30.2, U30.10
FB30: R154.2, SJ31.2, U31.10
FB31: R159.2, SJ32.2, U32.10
FB32: R164.2, SJ33.2, U33.10
FB33: R169.2, SJ34.2, U34.10
FB34: R174.2, SJ35.2, U35.10
FB35: R179.2, SJ36.2, U36.10
FB36: R184.2, SJ37.2, U37.10
FB37: R189.2, SJ38.2, U38.10
FB38: R194.2, SJ39.2, U39.10
FB39: R199.2, SJ40.2, U40.10
FB40: R204.2, SJ41.2, U41.10
FB41: R209.2, SJ42.2, U42.10
FB42: R214.2, SJ43.2, U43.10
FB43: R219.2, SJ44.2, U44.10
FB44: R224.2, SJ45.2, U45.10
FB45: R229.2, SJ46.2, U46.10
FB46: R234.2, SJ47.2, U47.10
FB47: R239.2, SJ48.2, U48.10
FB48: R244.2, SJ49.2, U49.10
FB49: R249.2, SJ50.2, U50.10
FB50: R254.2, SJ51.2, U51.10
FB51: R259.2, SJ52.2, U52.10
FB52: R264.2, SJ53.2, U53.10
FB53: R269.2, SJ54.2, U54.10
FB54: R274.2, SJ55.2, U55.10
FB55: R279.2, SJ56.2, U56.10
FB56: R284.2, SJ57.2, U57.10
FB57: R289.2, SJ58.2, U58.10
FB58: R294.2, SJ59.2, U59.10
FB59: R299.2, SJ60.2, U60.10
FB60: R304.2, SJ61.2, U61.10
FB61: R309.2, SJ62.2, U62.10
FB62: R314.2, SJ63.2, U63.10
FB63: R319.2, SJ64.2, U64.10
GND: C1.2, C3.2, C4.2, JP1.1, JP3.1, JP7.1, R4.1, R6.1, U1.4, U1.9, U1.11, U1.12, U1.13, U1.14, U1.15
GND1: C5.2, C7.2, C8.2, JP8.1, JP9.1, JP14.1, R2.1, R9.1, U2.4, U2.9, U2.11, U2.12, U2.13, U2.14, U2.15
GND2: C9.2, C11.2, C12.2, JP15.1, JP16.1, JP21.1, R12.1, R14.1, U3.4, U3.9, U3.11, U3.12, U3.13, U3.14, U3.15
GND3: C13.2, C15.2, C16.2, JP22.1, JP23.1, JP28.1, R17.1, R19.1, U4.4, U4.9, U4.11, U4.12, U4.13, U4.14, U4.15
GND4: C17.2, C19.2, C20.2, JP29.1, JP30.1, JP35.1, R22.1, R24.1, U5.4, U5.9, U5.11, U5.12, U5.13, U5.14, U5.15
GND5: C21.2, C23.2, C24.2, JP36.1, JP37.1, JP42.1, R27.1, R29.1, U6.4, U6.9, U6.11, U6.12, U6.13, U6.14, U6.15
GND6: C25.2, C27.2, C28.2, JP43.1, JP44.1, JP49.1, R32.1, R34.1, U7.4, U7.9, U7.11, U7.12, U7.13, U7.14, U7.15
GND7: C29.2, C31.2, C32.2, JP50.1, JP51.1, JP56.1, R37.1, R39.1, U8.4, U8.9, U8.11, U8.12, U8.13, U8.14, U8.15
GND8: C33.2, C35.2, C36.2, JP57.1, JP58.1, JP63.1, R42.1, R44.1, U9.4, U9.9, U9.11, U9.12, U9.13, U9.14, U9.15
GND9: C37.2, C39.2, C40.2, JP64.1, JP65.1, JP70.1, R47.1, R49.1, U10.4, U10.9, U10.11, U10.12, U10.13, U10.14, U10.15
GND10: C41.2, C43.2, C44.2, JP71.1, JP72.1, JP77.1, R52.1, R54.1, U11.4, U11.9, U11.11, U11.12, U11.13, U11.14, U11.15
GND11: C45.2, C47.2, C48.2, JP78.1, JP79.1, JP84.1, R57.1, R59.1, U12.4, U12.9, U12.11, U12.12, U12.13, U12.14, U12.15
GND12: C49.2, C51.2, C52.2, JP85.1, JP86.1, JP91.1, R62.1, R64.1, U13.4, U13.9, U13.11, U13.12, U13.13, U13.14, U13.15
GND13: C53.2, C55.2, C56.2, JP92.1, JP93.1, JP98.1, R67.1, R69.1, U14.4, U14.9, U14.11, U14.12, U14.13, U14.14, U14.15
GND14: C57.2, C59.2, C60.2, JP99.1, JP100.1, JP105.1, R72.1, R74.1, U15.4, U15.9, U15.11, U15.12, U15.13, U15.14, U15.15
GND15: C61.2, C63.2, C64.2, JP106.1, JP107.1, JP112.1, R77.1, R79.1, U16.4, U16.9, U16.11, U16.12, U16.13, U16.14, U16.15
GND16: C65.2, C67.2, C68.2, JP113.1, JP114.1, JP119.1, R82.1, R84.1, U17.4, U17.9, U17.11, U17.12, U17.13, U17.14, U17.15
GND17: C69.2, C71.2, C72.2, JP120.1, JP121.1, JP126.1, R87.1, R89.1, U18.4, U18.9, U18.11, U18.12, U18.13, U18.14, U18.15
GND18: C73.2, C75.2, C76.2, JP127.1, JP128.1, JP133.1, R92.1, R94.1, U19.4, U19.9, U19.11, U19.12, U19.13, U19.14, U19.15
GND19: C77.2, C79.2, C80.2, JP134.1, JP135.1, JP140.1, R97.1, R99.1, U20.4, U20.9, U20.11, U20.12, U20.13, U20.14, U20.15
GND20: C81.2, C83.2, C84.2, JP141.1, JP142.1, JP147.1, R102.1, R104.1, U21.4, U21.9, U21.11, U21.12, U21.13, U21.14, U21.15
GND21: C85.2, C87.2, C88.2, JP148.1, JP149.1, JP154.1, R107.1, R109.1, U22.4, U22.9, U22.11, U22.12, U22.13, U22.14, U22.15
GND22: C89.2, C91.2, C92.2, JP155.1, JP156.1, JP161.1, R112.1, R114.1, U23.4, U23.9, U23.11, U23.12, U23.13, U23.14, U23.15
GND23: C93.2, C95.2, C96.2, JP162.1, JP163.1, JP168.1, R117.1, R119.1, U24.4, U24.9, U24.11, U24.12, U24.13, U24.14, U24.15
GND24: C97.2, C99.2, C100.2, JP169.1, JP170.1, JP175.1, R122.1, R124.1, U25.4, U25.9, U25.11, U25.12, U25.13, U25.14, U25.15
GND25: C101.2, C103.2, C104.2, JP176.1, JP177.1, JP182.1, R127.1, R129.1, U26.4, U26.9, U26.11, U26.12, U26.13, U26.14, U26.15
GND26: C105.2, C107.2, C108.2, JP183.1, JP184.1, JP189.1, R132.1, R134.1, U27.4, U27.9, U27.11, U27.12, U27.13, U27.14, U27.15
GND27: C109.2, C111.2, C112.2, JP190.1, JP191.1, JP196.1, R137.1, R139.1, U28.4, U28.9, U28.11, U28.12, U28.13, U28.14, U28.15
GND28: C113.2, C115.2, C116.2, JP197.1, JP198.1, JP203.1, R142.1, R144.1, U29.4, U29.9, U29.11, U29.12, U29.13, U29.14, U29.15
GND29: C117.2, C119.2, C120.2, JP204.1, JP205.1, JP210.1, R147.1, R149.1, U30.4, U30.9, U30.11, U30.12, U30.13, U30.14, U30.15
GND30: C121.2, C123.2, C124.2, JP211.1, JP212.1, JP217.1, R152.1, R154.1, U31.4, U31.9, U31.11, U31.12, U31.13, U31.14, U31.15
GND31: C125.2, C127.2, C128.2, JP218.1, JP219.1, JP224.1, R157.1, R159.1, U32.4, U32.9, U32.11, U32.12, U32.13, U32.14, U32.15
GND32: C129.2, C131.2, C132.2, JP225.1, JP226.1, JP231.1, R162.1, R164.1, U33.4, U33.9, U33.11, U33.12, U33.13, U33.14, U33.15
GND33: C133.2, C135.2, C136.2, JP232.1, JP233.1, JP238.1, R167.1, R169.1, U34.4, U34.9, U34.11, U34.12, U34.13, U34.14, U34.15
GND34: C137.2, C139.2, C140.2, JP239.1, JP240.1, JP245.1, R172.1, R174.1, U35.4, U35.9, U35.11, U35.12, U35.13, U35.14, U35.15
GND35: C141.2, C143.2, C144.2, JP246.1, JP247.1, JP252.1, R177.1, R179.1, U36.4, U36.9, U36.11, U36.12, U36.13, U36.14, U36.15
GND36: C145.2, C147.2, C148.2, JP253.1, JP254.1, JP259.1, R182.1, R184.1, U37.4, U37.9, U37.11, U37.12, U37.13, U37.14, U37.15
GND37: C149.2, C151.2, C152.2, JP260.1, JP261.1, JP266.1, R187.1, R189.1, U38.4, U38.9, U38.11, U38.12, U38.13, U38.14, U38.15
GND38: C153.2, C155.2, C156.2, JP267.1, JP268.1, JP273.1, R192.1, R194.1, U39.4, U39.9, U39.11, U39.12, U39.13, U39.14, U39.15
GND39: C157.2, C159.2, C160.2, JP274.1, JP275.1, JP280.1, R197.1, R199.1, U40.4, U40.9, U40.11, U40.12, U40.13, U40.14, U40.15
GND40: C161.2, C163.2, C164.2, JP281.1, JP282.1, JP287.1, R202.1, R204.1, U41.4, U41.9, U41.11, U41.12, U41.13, U41.14, U41.15
GND41: C165.2, C167.2, C168.2, JP288.1, JP289.1, JP294.1, R207.1, R209.1, U42.4, U42.9, U42.11, U42.12, U42.13, U42.14, U42.15
GND42: C169.2, C171.2, C172.2, JP295.1, JP296.1, JP301.1, R212.1, R214.1, U43.4, U43.9, U43.11, U43.12, U43.13, U43.14, U43.15
GND43: C173.2, C175.2, C176.2, JP302.1, JP303.1, JP308.1, R217.1, R219.1, U44.4, U44.9, U44.11, U44.12, U44.13, U44.14, U44.15
GND44: C177.2, C179.2, C180.2, JP309.1, JP310.1, JP315.1, R222.1, R224.1, U45.4, U45.9, U45.11, U45.12, U45.13, U45.14, U45.15
GND45: C181.2, C183.2, C184.2, JP316.1, JP317.1, JP322.1, R227.1, R229.1, U46.4, U46.9, U46.11, U46.12, U46.13, U46.14, U46.15
GND46: C185.2, C187.2, C188.2, JP323.1, JP324.1, JP329.1, R232.1, R234.1, U47.4, U47.9, U47.11, U47.12, U47.13, U47.14, U47.15
GND47: C189.2, C191.2, C192.2, JP330.1, JP331.1, JP336.1, R237.1, R239.1, U48.4, U48.9, U48.11, U48.12, U48.13, U48.14, U48.15
GND48: C193.2, C195.2, C196.2, JP337.1, JP338.1, JP343.1, R242.1, R244.1, U49.4, U49.9, U49.11, U49.12, U49.13, U49.14, U49.15
GND49: C197.2, C199.2, C200.2, JP344.1, JP345.1, JP350.1, R247.1, R249.1, U50.4, U50.9, U50.11, U50.12, U50.13, U50.14, U50.15
GND50: C201.2, C203.2, C204.2, JP351.1, JP352.1, JP357.1, R252.1, R254.1, U51.4, U51.9, U51.11, U51.12, U51.13, U51.14, U51.15
GND51: C205.2, C207.2, C208.2, JP358.1, JP359.1, JP364.1, R257.1, R259.1, U52.4, U52.9, U52.11, U52.12, U52.13, U52.14, U52.15
GND52: C209.2, C211.2, C212.2, JP365.1, JP366.1, JP371.1, R262.1, R264.1, U53.4, U53.9, U53.11, U53.12, U53.13, U53.14, U53.15
GND53: C213.2, C215.2, C216.2, JP372.1, JP373.1, JP378.1, R267.1, R269.1, U54.4, U54.9, U54.11, U54.12, U54.13, U54.14, U54.15
GND54: C217.2, C219.2, C220.2, JP379.1, JP380.1, JP385.1, R272.1, R274.1, U55.4, U55.9, U55.11, U55.12, U55.13, U55.14, U55.15
GND55: C221.2, C223.2, C224.2, JP386.1, JP387.1, JP392.1, R277.1, R279.1, U56.4, U56.9, U56.11, U56.12, U56.13, U56.14, U56.15
GND56: C225.2, C227.2, C228.2, JP393.1, JP394.1, JP399.1, R282.1, R284.1, U57.4, U57.9, U57.11, U57.12, U57.13, U57.14, U57.15
GND57: C229.2, C231.2, C232.2, JP400.1, JP401.1, JP406.1, R287.1, R289.1, U58.4, U58.9, U58.11, U58.12, U58.13, U58.14, U58.15
GND58: C233.2, C235.2, C236.2, JP407.1, JP408.1, JP413.1, R292.1, R294.1, U59.4, U59.9, U59.11, U59.12, U59.13, U59.14, U59.15
GND59: C237.2, C239.2, C240.2, JP414.1, JP415.1, JP420.1, R297.1, R299.1, U60.4, U60.9, U60.11, U60.12, U60.13, U60.14, U60.15
GND60: C241.2, C243.2, C244.2, JP421.1, JP422.1, JP427.1, R302.1, R304.1, U61.4, U61.9, U61.11, U61.12, U61.13, U61.14, U61.15
GND61: C245.2, C247.2, C248.2, JP428.1, JP429.1, JP434.1, R307.1, R309.1, U62.4, U62.9, U62.11, U62.12, U62.13, U62.14, U62.15
GND62: C249.2, C251.2, C252.2, JP435.1, JP436.1, JP441.1, R312.1, R314.1, U63.4, U63.9, U63.11, U63.12, U63.13, U63.14, U63.15
GND63: C253.2, C255.2, C256.2, JP442.1, JP443.1, JP448.1, R317.1, R319.1, U64.4, U64.9, U64.11, U64.12, U64.13, U64.14, U64.15
unnamed: C4.1, U1.1
unnamed: L1.P$1, U1.3
unnamed: L2.P$1, U2.3
unnamed: C7.1, U2.1
unnamed: L3.P$1, U3.3
unnamed: C11.1, U3.1
unnamed: L4.P$1, U4.3
unnamed: C15.1, U4.1
unnamed: L5.P$1, U5.3
unnamed: C19.1, U5.1
unnamed: L6.P$1, U6.3
unnamed: C23.1, U6.1
unnamed: L7.P$1, U7.3
unnamed: C27.1, U7.1
unnamed: L8.P$1, U8.3
unnamed: C31.1, U8.1
unnamed: L9.P$1, U9.3
unnamed: C35.1, U9.1
unnamed: L10.P$1, U10.3
unnamed: C39.1, U10.1
unnamed: L11.P$1, U11.3
unnamed: C43.1, U11.1
unnamed: L12.P$1, U12.3
unnamed: C47.1, U12.1
unnamed: L13.P$1, U13.3
unnamed: C51.1, U13.1
unnamed: L14.P$1, U14.3
unnamed: C55.1, U14.1
unnamed: L15.P$1, U15.3
unnamed: C59.1, U15.1
unnamed: L16.P$1, U16.3
unnamed: C63.1, U16.1
unnamed: L17.P$1, U17.3
unnamed: C67.1, U17.1
unnamed: L18.P$1, U18.3
unnamed: C71.1, U18.1
unnamed: L19.P$1, U19.3
unnamed: C75.1, U19.1
unnamed: L20.P$1, U20.3
unnamed: C79.1, U20.1
unnamed: L21.P$1, U21.3
unnamed: C83.1, U21.1
unnamed: L22.P$1, U22.3
unnamed: C87.1, U22.1
unnamed: L23.P$1, U23.3
unnamed: C91.1, U23.1
unnamed: L24.P$1, U24.3
unnamed: C95.1, U24.1
unnamed: L25.P$1, U25.3
unnamed: C99.1, U25.1
unnamed: L26.P$1, U26.3
unnamed: C103.1, U26.1
unnamed: L27.P$1, U27.3
unnamed: C107.1, U27.1
unnamed: L28.P$1, U28.3
unnamed: C111.1, U28.1
unnamed: L29.P$1, U29.3
unnamed: C115.1, U29.1
unnamed: L30.P$1, U30.3
unnamed: C119.1, U30.1
unnamed: L31.P$1, U31.3
unnamed: C123.1, U31.1
unnamed: L32.P$1, U32.3
unnamed: C127.1, U32.1
unnamed: L33.P$1, U33.3
unnamed: C131.1, U33.1
unnamed: L34.P$1, U34.3
unnamed: C135.1, U34.1
unnamed: L35.P$1, U35.3
unnamed: C139.1, U35.1
unnamed: L36.P$1, U36.3
unnamed: C143.1, U36.1
unnamed: L37.P$1, U37.3
unnamed: C147.1, U37.1
unnamed: L38.P$1, U38.3
unnamed: C151.1, U38.1
unnamed: L39.P$1, U39.3
unnamed: C155.1, U39.1
unnamed: L40.P$1, U40.3
unnamed: C159.1, U40.1
unnamed: L41.P$1, U41.3
unnamed: C163.1, U41.1
unnamed: L42.P$1, U42.3
unnamed: C167.1, U42.1
unnamed: L43.P$1, U43.3
unnamed: C171.1, U43.1
unnamed: L44.P$1, U44.3
unnamed: C175.1, U44.1
unnamed: L45.P$1, U45.3
unnamed: C179.1, U45.1
unnamed: L46.P$1, U46.3
unnamed: C183.1, U46.1
unnamed: L47.P$1, U47.3
unnamed: C187.1, U47.1
unnamed: L48.P$1, U48.3
unnamed: C191.1, U48.1
unnamed: L49.P$1, U49.3
unnamed: C195.1, U49.1
unnamed: L50.P$1, U50.3
unnamed: C199.1, U50.1
unnamed: L51.P$1, U51.3
unnamed: C203.1, U51.1
unnamed: L52.P$1, U52.3
unnamed: C207.1, U52.1
unnamed: L53.P$1, U53.3
unnamed: C211.1, U53.1
unnamed: L54.P$1, U54.3
unnamed: C215.1, U54.1
unnamed: L55.P$1, U55.3
unnamed: C219.1, U55.1
unnamed: L56.P$1, U56.3
unnamed: C223.1, U56.1
unnamed: L57.P$1, U57.3
unnamed: C227.1, U57.1
unnamed: L58.P$1, U58.3
unnamed: C231.1, U58.1
unnamed: L59.P$1, U59.3
unnamed: C235.1, U59.1
unnamed: L60.P$1, U60.3
unnamed: C239.1, U60.1
unnamed: L61.P$1, U61.3
unnamed: C243.1, U61.1
unnamed: L62.P$1, U62.3
unnamed: C247.1, U62.1
unnamed: L63.P$1, U63.3
unnamed: C251.1, U63.1
unnamed: L64.P$1, U64.3
unnamed: C255.1, U64.1
UVLO: C2.2, R3.1, R4.2, U1.7
UVLO1: C6.2, R1.1, R2.2, U2.7
UVLO2: C10.2, R11.1, R12.2, U3.7
UVLO3: C14.2, R16.1, R17.2, U4.7
UVLO4: C18.2, R21.1, R22.2, U5.7
UVLO5: C22.2, R26.1, R27.2, U6.7
UVLO6: C26.2, R31.1, R32.2, U7.7
UVLO7: C30.2, R36.1, R37.2, U8.7
UVLO8: C34.2, R41.1, R42.2, U9.7
UVLO9: C38.2, R46.1, R47.2, U10.7
UVLO10: C42.2, R51.1, R52.2, U11.7
UVLO11: C46.2, R56.1, R57.2, U12.7
UVLO12: C50.2, R61.1, R62.2, U13.7
UVLO13: C54.2, R66.1, R67.2, U14.7
UVLO14: C58.2, R71.1, R72.2, U15.7
UVLO15: C62.2, R76.1, R77.2, U16.7
UVLO16: C66.2, R81.1, R82.2, U17.7
UVLO17: C70.2, R86.1, R87.2, U18.7
UVLO18: C74.2, R91.1, R92.2, U19.7
UVLO19: C78.2, R96.1, R97.2, U20.7
UVLO20: C82.2, R101.1, R102.2, U21.7
UVLO21: C86.2, R106.1, R107.2, U22.7
UVLO22: C90.2, R111.1, R112.2, U23.7
UVLO23: C94.2, R116.1, R117.2, U24.7
UVLO24: C98.2, R121.1, R122.2, U25.7
UVLO25: C102.2, R126.1, R127.2, U26.7
UVLO26: C106.2, R131.1, R132.2, U27.7
UVLO27: C110.2, R136.1, R137.2, U28.7
UVLO28: C114.2, R141.1, R142.2, U29.7
UVLO29: C118.2, R146.1, R147.2, U30.7
UVLO30: C122.2, R151.1, R152.2, U31.7
UVLO31: C126.2, R156.1, R157.2, U32.7
UVLO32: C130.2, R161.1, R162.2, U33.7
UVLO33: C134.2, R166.1, R167.2, U34.7
UVLO34: C138.2, R171.1, R172.2, U35.7
UVLO35: C142.2, R176.1, R177.2, U36.7
UVLO36: C146.2, R181.1, R182.2, U37.7
UVLO37: C150.2, R186.1, R187.2, U38.7
UVLO38: C154.2, R191.1, R192.2, U39.7
UVLO39: C158.2, R196.1, R197.2, U40.7
UVLO40: C162.2, R201.1, R202.2, U41.7
UVLO41: C166.2, R206.1, R207.2, U42.7
UVLO42: C170.2, R211.1, R212.2, U43.7
UVLO43: C174.2, R216.1, R217.2, U44.7
UVLO44: C178.2, R221.1, R222.2, U45.7
UVLO45: C182.2, R226.1, R227.2, U46.7
UVLO46: C186.2, R231.1, R232.2, U47.7
UVLO47: C190.2, R236.1, R237.2, U48.7
UVLO48: C194.2, R241.1, R242.2, U49.7
UVLO49: C198.2, R246.1, R247.2, U50.7
UVLO50: C202.2, R251.1, R252.2, U51.7
UVLO51: C206.2, R256.1, R257.2, U52.7
UVLO52: C210.2, R261.1, R262.2, U53.7
UVLO53: C214.2, R266.1, R267.2, U54.7
UVLO54: C218.2, R271.1, R272.2, U55.7
UVLO55: C222.2, R276.1, R277.2, U56.7
UVLO56: C226.2, R281.1, R282.2, U57.7
UVLO57: C230.2, R286.1, R287.2, U58.7
UVLO58: C234.2, R291.1, R292.2, U59.7
UVLO59: C238.2, R296.1, R297.2, U60.7
UVLO60: C242.2, R301.1, R302.2, U61.7
UVLO61: C246.2, R306.1, R307.2, U62.7
UVLO62: C250.2, R311.1, R312.2, U63.7
UVLO63: C254.2, R316.1, R317.2, U64.7
VCC: C3.1, JP1.2, R5.2, R7.2, U1.2
VCC1: C5.1, JP9.2, R8.2, R10.2, U2.2
VCC2: C9.1, JP16.2, R13.2, R15.2, U3.2
VCC3: C13.1, JP23.2, R18.2, R20.2, U4.2
VCC4: C17.1, JP30.2, R23.2, R25.2, U5.2
VCC5: C21.1, JP37.2, R28.2, R30.2, U6.2
VCC6: C25.1, JP44.2, R33.2, R35.2, U7.2
VCC7: C29.1, JP51.2, R38.2, R40.2, U8.2
VCC8: C33.1, JP58.2, R43.2, R45.2, U9.2
VCC9: C37.1, JP65.2, R48.2, R50.2, U10.2
VCC10: C41.1, JP72.2, R53.2, R55.2, U11.2
VCC11: C45.1, JP79.2, R58.2, R60.2, U12.2
VCC12: C49.1, JP86.2, R63.2, R65.2, U13.2
VCC13: C53.1, JP93.2, R68.2, R70.2, U14.2
VCC14: C57.1, JP100.2, R73.2, R75.2, U15.2
VCC15: C61.1, JP107.2, R78.2, R80.2, U16.2
VCC16: C65.1, JP114.2, R83.2, R85.2, U17.2
VCC17: C69.1, JP121.2, R88.2, R90.2, U18.2
VCC18: C73.1, JP128.2, R93.2, R95.2, U19.2
VCC19: C77.1, JP135.2, R98.2, R100.2, U20.2
VCC20: C81.1, JP142.2, R103.2, R105.2, U21.2
VCC21: C85.1, JP149.2, R108.2, R110.2, U22.2
VCC22: C89.1, JP156.2, R113.2, R115.2, U23.2
VCC23: C93.1, JP163.2, R118.2, R120.2, U24.2
VCC24: C97.1, JP170.2, R123.2, R125.2, U25.2
VCC25: C101.1, JP177.2, R128.2, R130.2, U26.2
VCC26: C105.1, JP184.2, R133.2, R135.2, U27.2
VCC27: C109.1, JP191.2, R138.2, R140.2, U28.2
VCC28: C113.1, JP198.2, R143.2, R145.2, U29.2
VCC29: C117.1, JP205.2, R148.2, R150.2, U30.2
VCC30: C121.1, JP212.2, R153.2, R155.2, U31.2
VCC31: C125.1, JP219.2, R158.2, R160.2, U32.2
VCC32: C129.1, JP226.2, R163.2, R165.2, U33.2
VCC33: C133.1, JP233.2, R168.2, R170.2, U34.2
VCC34: C137.1, JP240.2, R173.2, R175.2, U35.2
VCC35: C141.1, JP247.2, R178.2, R180.2, U36.2
VCC36: C145.1, JP254.2, R183.2, R185.2, U37.2
VCC37: C149.1, JP261.2, R188.2, R190.2, U38.2
VCC38: C153.1, JP268.2, R193.2, R195.2, U39.2
VCC39: C157.1, JP275.2, R198.2, R200.2, U40.2
VCC40: C161.1, JP282.2, R203.2, R205.2, U41.2
VCC41: C165.1, JP289.2, R208.2, R210.2, U42.2
VCC42: C169.1, JP296.2, R213.2, R215.2, U43.2
VCC43: C173.1, JP303.2, R218.2, R220.2, U44.2
VCC44: C177.1, JP310.2, R223.2, R225.2, U45.2
VCC45: C181.1, JP317.2, R228.2, R230.2, U46.2
VCC46: C185.1, JP324.2, R233.2, R235.2, U47.2
VCC47: C189.1, JP331.2, R238.2, R240.2, U48.2
VCC48: C193.1, JP338.2, R243.2, R245.2, U49.2
VCC49: C197.1, JP345.2, R248.2, R250.2, U50.2
VCC50: C201.1, JP352.2, R253.2, R255.2, U51.2
VCC51: C205.1, JP359.2, R258.2, R260.2, U52.2
VCC52: C209.1, JP366.2, R263.2, R265.2, U53.2
VCC53: C213.1, JP373.2, R268.2, R270.2, U54.2
VCC54: C217.1, JP380.2, R273.2, R275.2, U55.2
VCC55: C221.1, JP387.2, R278.2, R280.2, U56.2
VCC56: C225.1, JP394.2, R283.2, R285.2, U57.2
VCC57: C229.1, JP401.2, R288.2, R290.2, U58.2
VCC58: C233.1, JP408.2, R293.2, R295.2, U59.2
VCC59: C237.1, JP415.2, R298.2, R300.2, U60.2
VCC60: C241.1, JP422.2, R303.2, R305.2, U61.2
VCC61: C245.1, JP429.2, R308.2, R310.2, U62.2
VCC62: C249.1, JP436.2, R313.2, R315.2, U63.2
VCC63: C253.1, JP443.2, R318.2, R320.2, U64.2
VIN: C1.1, C2.1, JP3.2, JP7.2, L1.P$2, R3.2, U1.5, U1.6, U1.8
VIN1: C6.1, C8.1, JP8.2, JP14.2, L2.P$2, R1.2, U2.5, U2.6, U2.8
VIN2: C10.1, C12.1, JP15.2, JP21.2, L3.P$2, R11.2, U3.5, U3.6, U3.8
VIN3: C14.1, C16.1, JP22.2, JP28.2, L4.P$2, R16.2, U4.5, U4.6, U4.8
VIN4: C18.1, C20.1, JP29.2, JP35.2, L5.P$2, R21.2, U5.5, U5.6, U5.8
VIN5: C22.1, C24.1, JP36.2, JP42.2, L6.P$2, R26.2, U6.5, U6.6, U6.8
VIN6: C26.1, C28.1, JP43.2, JP49.2, L7.P$2, R31.2, U7.5, U7.6, U7.8
VIN7: C30.1, C32.1, JP50.2, JP56.2, L8.P$2, R36.2, U8.5, U8.6, U8.8
VIN8: C34.1, C36.1, JP57.2, JP63.2, L9.P$2, R41.2, U9.5, U9.6, U9.8
VIN9: C38.1, C40.1, JP64.2, JP70.2, L10.P$2, R46.2, U10.5, U10.6, U10.8
VIN10: C42.1, C44.1, JP71.2, JP77.2, L11.P$2, R51.2, U11.5, U11.6, U11.8
VIN11: C46.1, C48.1, JP78.2, JP84.2, L12.P$2, R56.2, U12.5, U12.6, U12.8
VIN12: C50.1, C52.1, JP85.2, JP91.2, L13.P$2, R61.2, U13.5, U13.6, U13.8
VIN13: C54.1, C56.1, JP92.2, JP98.2, L14.P$2, R66.2, U14.5, U14.6, U14.8
VIN14: C58.1, C60.1, JP99.2, JP105.2, L15.P$2, R71.2, U15.5, U15.6, U15.8
VIN15: C62.1, C64.1, JP106.2, JP112.2, L16.P$2, R76.2, U16.5, U16.6, U16.8
VIN16: C66.1, C68.1, JP113.2, JP119.2, L17.P$2, R81.2, U17.5, U17.6, U17.8
VIN17: C70.1, C72.1, JP120.2, JP126.2, L18.P$2, R86.2, U18.5, U18.6, U18.8
VIN18: C74.1, C76.1, JP127.2, JP133.2, L19.P$2, R91.2, U19.5, U19.6, U19.8
VIN19: C78.1, C80.1, JP134.2, JP140.2, L20.P$2, R96.2, U20.5, U20.6, U20.8
VIN20: C82.1, C84.1, JP141.2, JP147.2, L21.P$2, R101.2, U21.5, U21.6, U21.8
VIN21: C86.1, C88.1, JP148.2, JP154.2, L22.P$2, R106.2, U22.5, U22.6, U22.8
VIN22: C90.1, C92.1, JP155.2, JP161.2, L23.P$2, R111.2, U23.5, U23.6, U23.8
VIN23: C94.1, C96.1, JP162.2, JP168.2, L24.P$2, R116.2, U24.5, U24.6, U24.8
VIN24: C98.1, C100.1, JP169.2, JP175.2, L25.P$2, R121.2, U25.5, U25.6, U25.8
VIN25: C102.1, C104.1, JP176.2, JP182.2, L26.P$2, R126.2, U26.5, U26.6, U26.8
VIN26: C106.1, C108.1, JP183.2, JP189.2, L27.P$2, R131.2, U27.5, U27.6, U27.8
VIN27: C110.1, C112.1, JP190.2, JP196.2, L28.P$2, R136.2, U28.5, U28.6, U28.8
VIN28: C114.1, C116.1, JP197.2, JP203.2, L29.P$2, R141.2, U29.5, U29.6, U29.8
VIN29: C118.1, C120.1, JP204.2, JP210.2, L30.P$2, R146.2, U30.5, U30.6, U30.8
VIN30: C122.1, C124.1, JP211.2, JP217.2, L31.P$2, R151.2, U31.5, U31.6, U31.8
VIN31: C126.1, C128.1, JP218.2, JP224.2, L32.P$2, R156.2, U32.5, U32.6, U32.8
VIN32: C130.1, C132.1, JP225.2, JP231.2, L33.P$2, R161.2, U33.5, U33.6, U33.8
VIN33: C134.1, C136.1, JP232.2, JP238.2, L34.P$2, R166.2, U34.5, U34.6, U34.8
VIN34: C138.1, C140.1, JP239.2, JP245.2, L35.P$2, R171.2, U35.5, U35.6, U35.8
VIN35: C142.1, C144.1, JP246.2, JP252.2, L36.P$2, R176.2, U36.5, U36.6, U36.8
VIN36: C146.1, C148.1, JP253.2, JP259.2, L37.P$2, R181.2, U37.5, U37.6, U37.8
VIN37: C150.1, C152.1, JP260.2, JP266.2, L38.P$2, R186.2, U38.5, U38.6, U38.8
VIN38: C154.1, C156.1, JP267.2, JP273.2, L39.P$2, R191.2, U39.5, U39.6, U39.8
VIN39: C158.1, C160.1, JP274.2, JP280.2, L40.P$2, R196.2, U40.5, U40.6, U40.8
VIN40: C162.1, C164.1, JP281.2, JP287.2, L41.P$2, R201.2, U41.5, U41.6, U41.8
VIN41: C166.1, C168.1, JP288.2, JP294.2, L42.P$2, R206.2, U42.5, U42.6, U42.8
VIN42: C170.1, C172.1, JP295.2, JP301.2, L43.P$2, R211.2, U43.5, U43.6, U43.8
VIN43: C174.1, C176.1, JP302.2, JP308.2, L44.P$2, R216.2, U44.5, U44.6, U44.8
VIN44: C178.1, C180.1, JP309.2, JP315.2, L45.P$2, R221.2, U45.5, U45.6, U45.8
VIN45: C182.1, C184.1, JP316.2, JP322.2, L46.P$2, R226.2, U46.5, U46.6, U46.8
VIN46: C186.1, C188.1, JP323.2, JP329.2, L47.P$2, R231.2, U47.5, U47.6, U47.8
VIN47: C190.1, C192.1, JP330.2, JP336.2, L48.P$2, R236.2, U48.5, U48.6, U48.8
VIN48: C194.1, C196.1, JP337.2, JP343.2, L49.P$2, R241.2, U49.5, U49.6, U49.8
VIN49: C198.1, C200.1, JP344.2, JP350.2, L50.P$2, R246.2, U50.5, U50.6, U50.8
VIN50: C202.1, C204.1, JP351.2, JP357.2, L51.P$2, R251.2, U51.5, U51.6, U51.8
VIN51: C206.1, C208.1, JP358.2, JP364.2, L52.P$2, R256.2, U52.5, U52.6, U52.8
VIN52: C210.1, C212.1, JP365.2, JP371.2, L53.P$2, R261.2, U53.5, U53.6, U53.8
VIN53: C214.1, C216.1, JP372.2, JP378.2, L54.P$2, R266.2, U54.5, U54.6, U54.8
VIN54: C218.1, C220.1, JP379.2, JP385.2, L55.P$2, R271.2, U55.5, U55.6, U55.8
VIN55: C222.1, C224.1, JP386.2, JP392.2, L56.P$2, R276.2, U56.5, U56.6, U56.8
VIN56: C226.1, C228.1, JP393.2, JP399.2, L57.P$2, R281.2, U57.5, U57.6, U57.8
VIN57: C230.1, C232.1, JP400.2, JP406.2, L58.P$2, R286.2, U58.5, U58.6, U58.8
VIN58: C234.1, C236.1, JP407.2, JP413.2, L59.P$2, R291.2, U59.5, U59.6, U59.8
VIN59: C238.1, C240.1, JP414.2, JP420.2, L60.P$2, R296.2, U60.5, U60.6, U60.8
VIN60: C242.1, C244.1, JP421.2, JP427.2, L61.P$2, R301.2, U61.5, U61.6, U61.8
VIN61: C246.1, C248.1, JP428.2, JP434.2, L62.P$2, R306.2, U62.5, U62.6, U62.8
VIN62: C250.1, C252.1, JP435.2, JP441.2, L63.P$2, R311.2, U63.5, U63.6, U63.8
VIN63: C254.1, C256.1, JP442.2, JP448.2, L64.P$2, R316.2, U64.5, U64.6, U64.8
