individual61/flamingo-repo/Code/Flamingo - Nano BLE 33 Sensor/include/buttons.h

#ifndef BUTTONS_H
#define BUTTONS_H

//void button1PressAction(void);

//void button2PressAction(void);

//void checkButton1(void);

//void checkButton2(void);

//void setFullBrightnessOn10(void);

void isr_handler_A(void);

void isr_handler_B(void);

void isr_handler_C(void);

#endif
