individual61/flamingo-repo/Code/Bike Flamingo/include/bouncing_balls.h

#ifndef BOUNCING_BALLS_H
#define BOUNCING_BALLS_H

#include <Arduino.h>
#include <FastLED.h>

typedef struct bouncingball
{
  float position = 0.0;
  float mass = 0.0;
  float velocity = 0.0;
  uint16_t timeold = 0;
  uint16_t timenow = 0;
  CRGB colour = CRGB(255, 255, 255);
} bouncingball;

float eval_v_func_BB(float v, float x, float acc_ext, float damping,
                     float mass);
float get_next_v_BB(float oldv, float oldx, float acc_ext, float damping,
                    float mass);

                    float get_next_x_BB(float timestep_f, float oldv, float oldx);

void updateBallPosition_BB(bouncingball* theBall, float damping);

// float get_next_x(float oldv, float oldx) // defined in DHO

int ballToStrandPosition_BB(float ballPos_BB);

float getBallPosition_BB(float oldpos, float oldvel, float mass, float damping);

#endif
